houmei/MZ-80K/img/03RAM.png

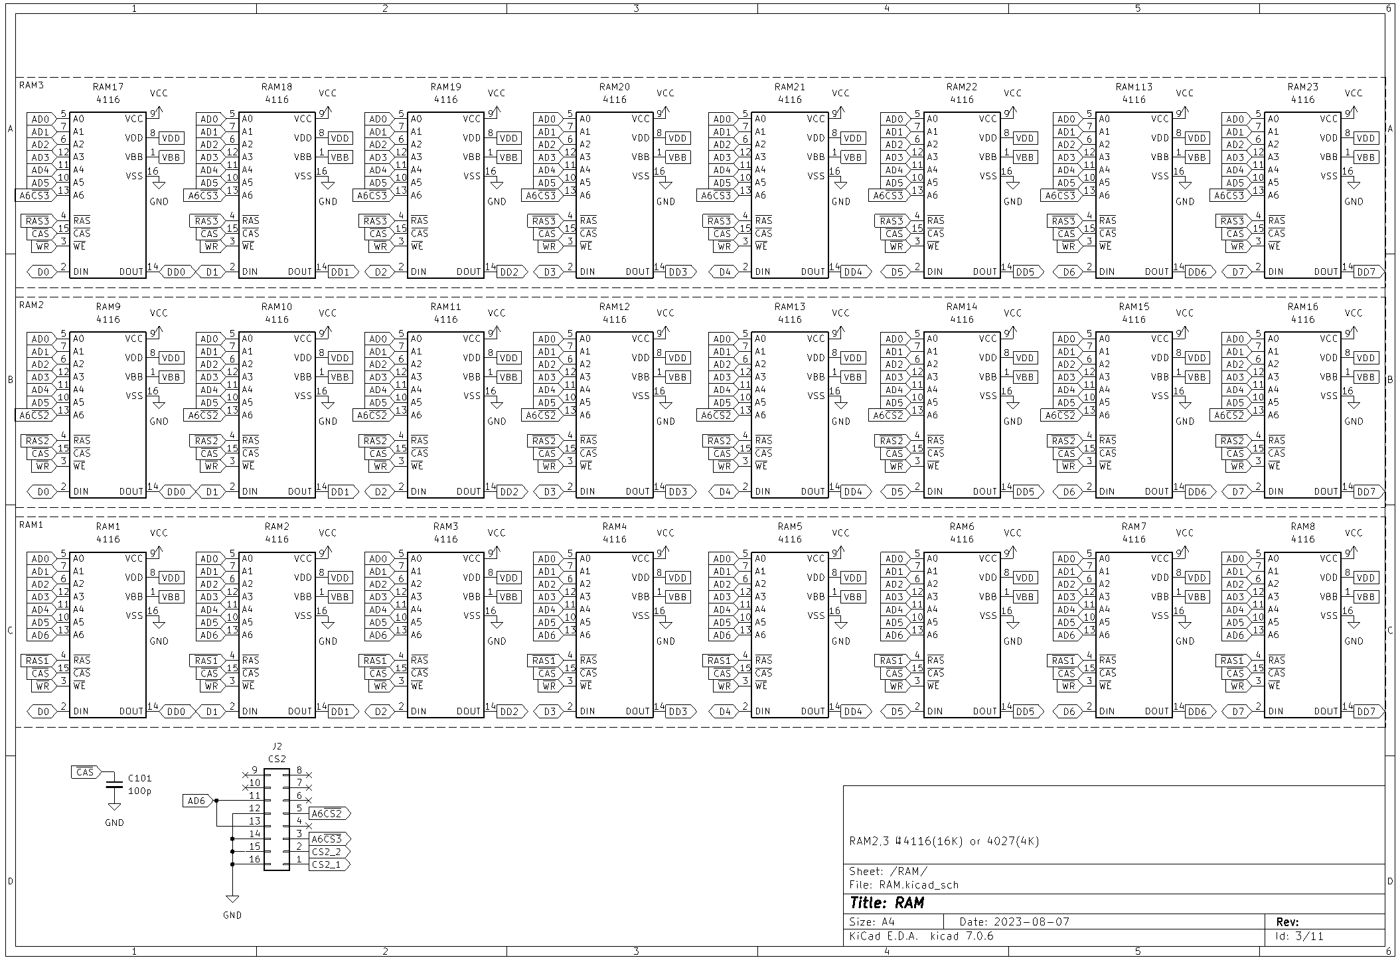
img/03RAM.png
