houmei/MZ-80K/img/05DECODE.png

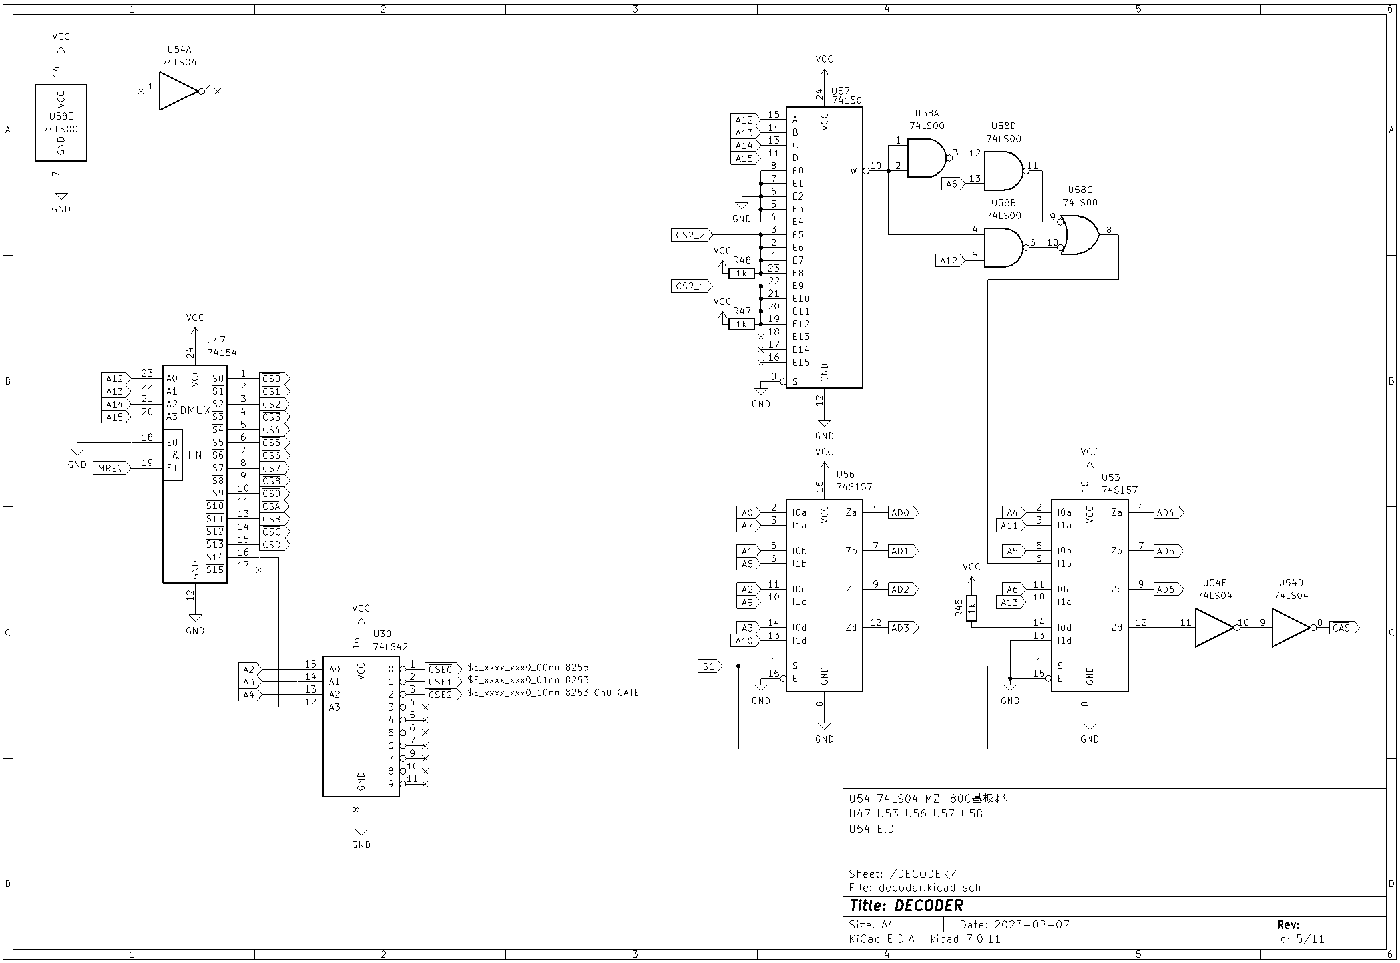
img/05DECODE.png
