houmei/MZ-80K/img/06SYNC.png

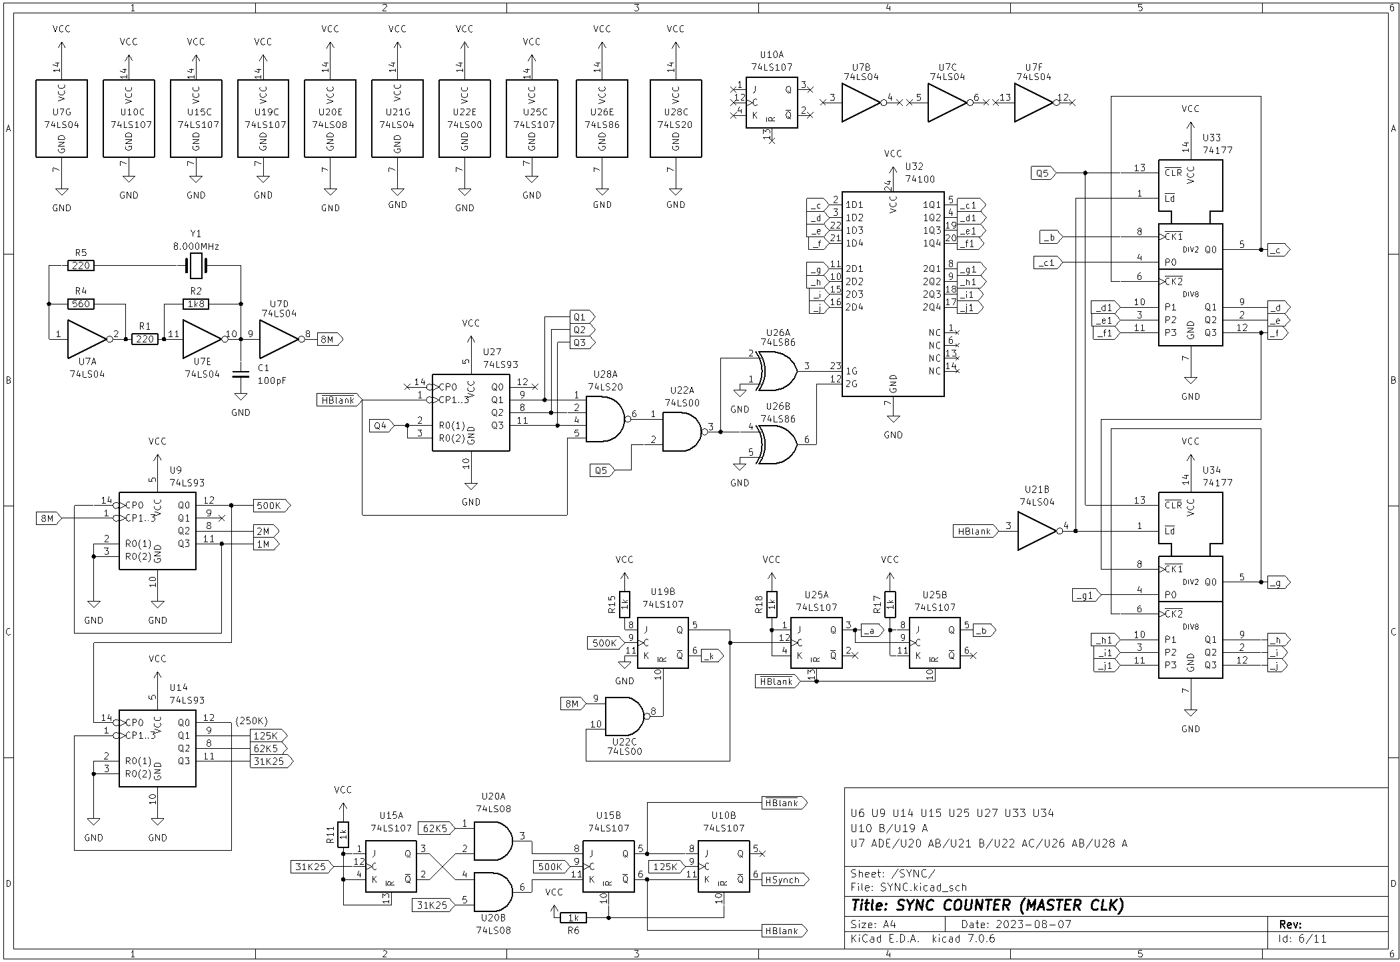
img/06SYNC.png
