houmei/MZ-80K/img/11CONN.png

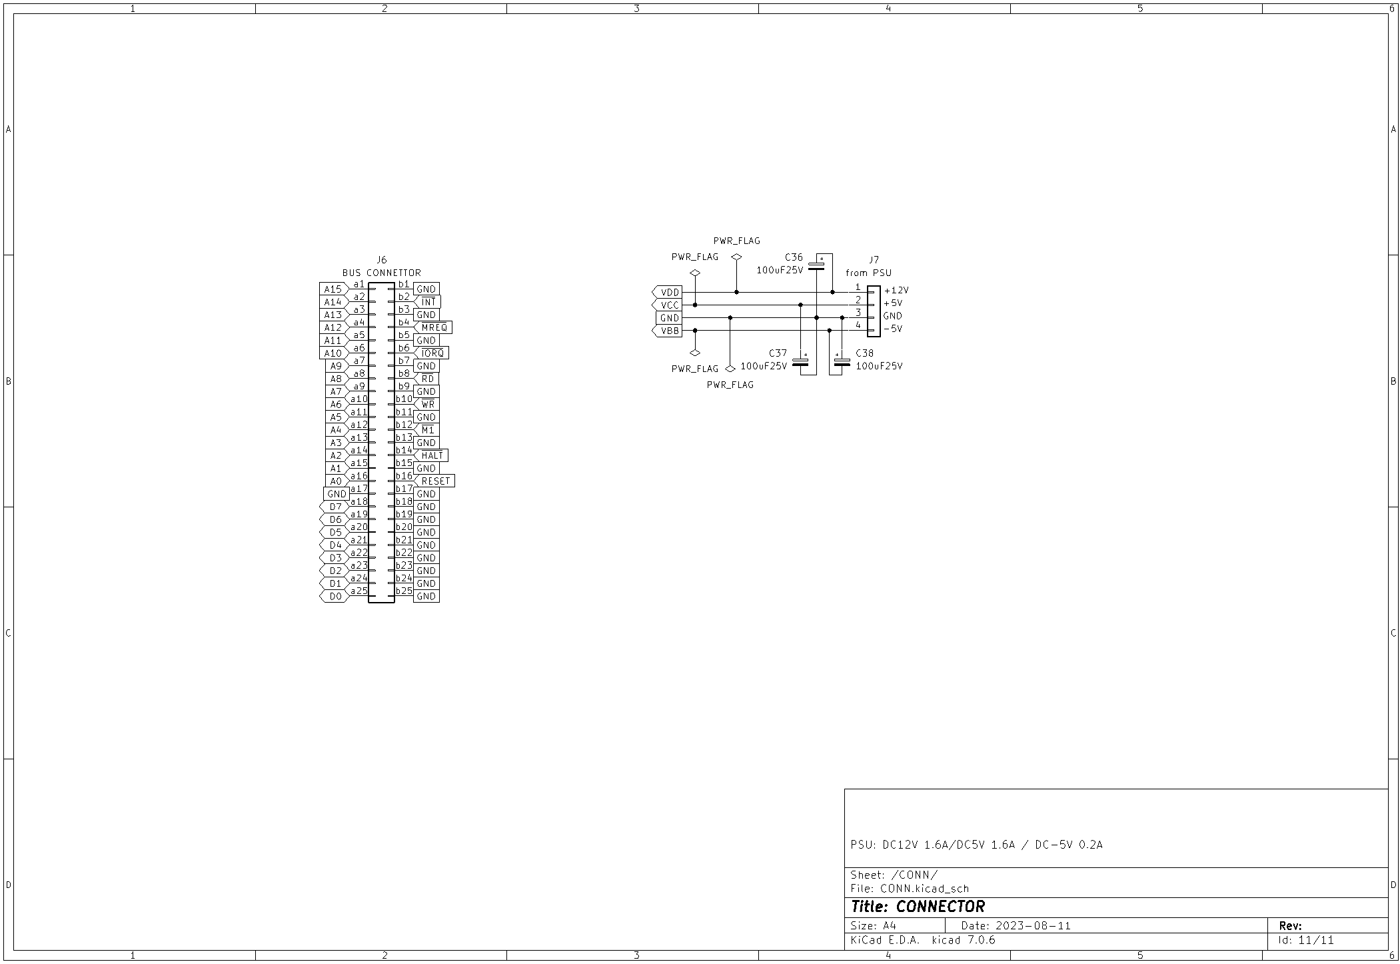
img/11CONN.png
