houmei/MZ-80K/MZ80KiCad/CONN.kicad_sch

## KiCad design MZ80KiCad/CONN.kicad_sch (2023-08-20)

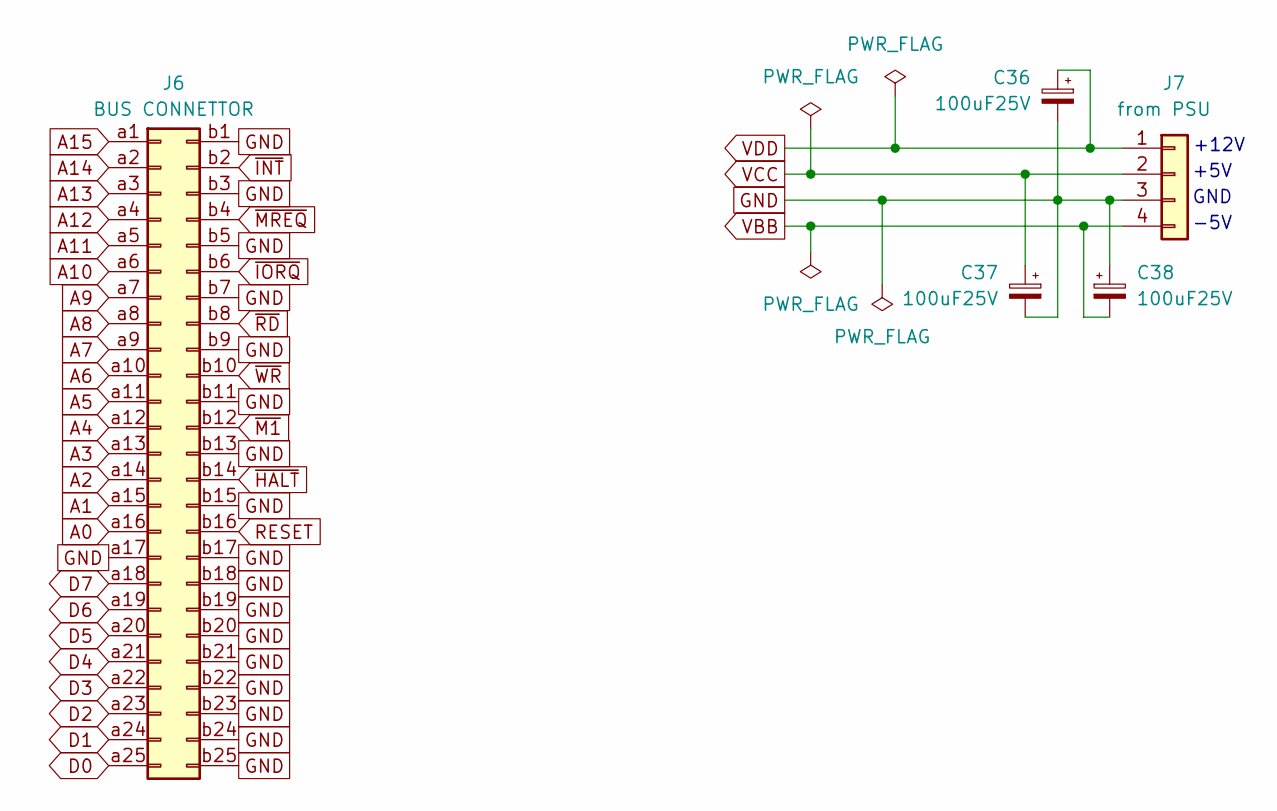
[picture p22: schematic CONN.kicad_sch]

Parts:
C36, C37, C38: 100uF25V
J6: BUS CONNETTOR; PinHeader_2x26_P2.54mm_Horizontal
J7: from PSU; PinHeader_1x04_P2.54mm_Vertical

Connections:
A0: J6.a16
A1: J6.a15
A2: J6.a14
A3: J6.a13
A4: J6.a12
A5: J6.a11
A6: J6.a10
A7: J6.a9
A8: J6.a8
A9: J6.a7
A10: J6.a6
A11: J6.a5
A12: J6.a4
A13: J6.a3
A14: J6.a2
A15: J6.a1
D0: J6.a25
D1: J6.a24
D2: J6.a23
D3: J6.a22
D4: J6.a21
D5: J6.a20
D6: J6.a19
D7: J6.a18
GND: C36.2, C37.2, C38.1, J6.a17, J6.b1, J6.b3, J6.b5, J6.b7, J6.b9, J6.b11, J6.b13, J6.b15, J6.b17, J6.b18, J6.b19, J6.b20, J6.b21, J6.b22, J6.b23, J6.b24, J6.b25, J7.3
RESET: J6.b16
VBB: C38.2, J7.4
VCC: C37.1, J7.2
VDD: C36.1, J7.1
~HALT: J6.b14
~INT: J6.b2
~IORQ: J6.b6
~M1: J6.b12
~MREQ: J6.b4
~RD: J6.b8
~WR: J6.b10

Notes on the sheet:
+5V
+12V
-5V
GND
