houmei/MZ-80K/MZ80KiCad/CPU.kicad_sch

## KiCad design MZ80KiCad/CPU.kicad_sch (2024-05-27)

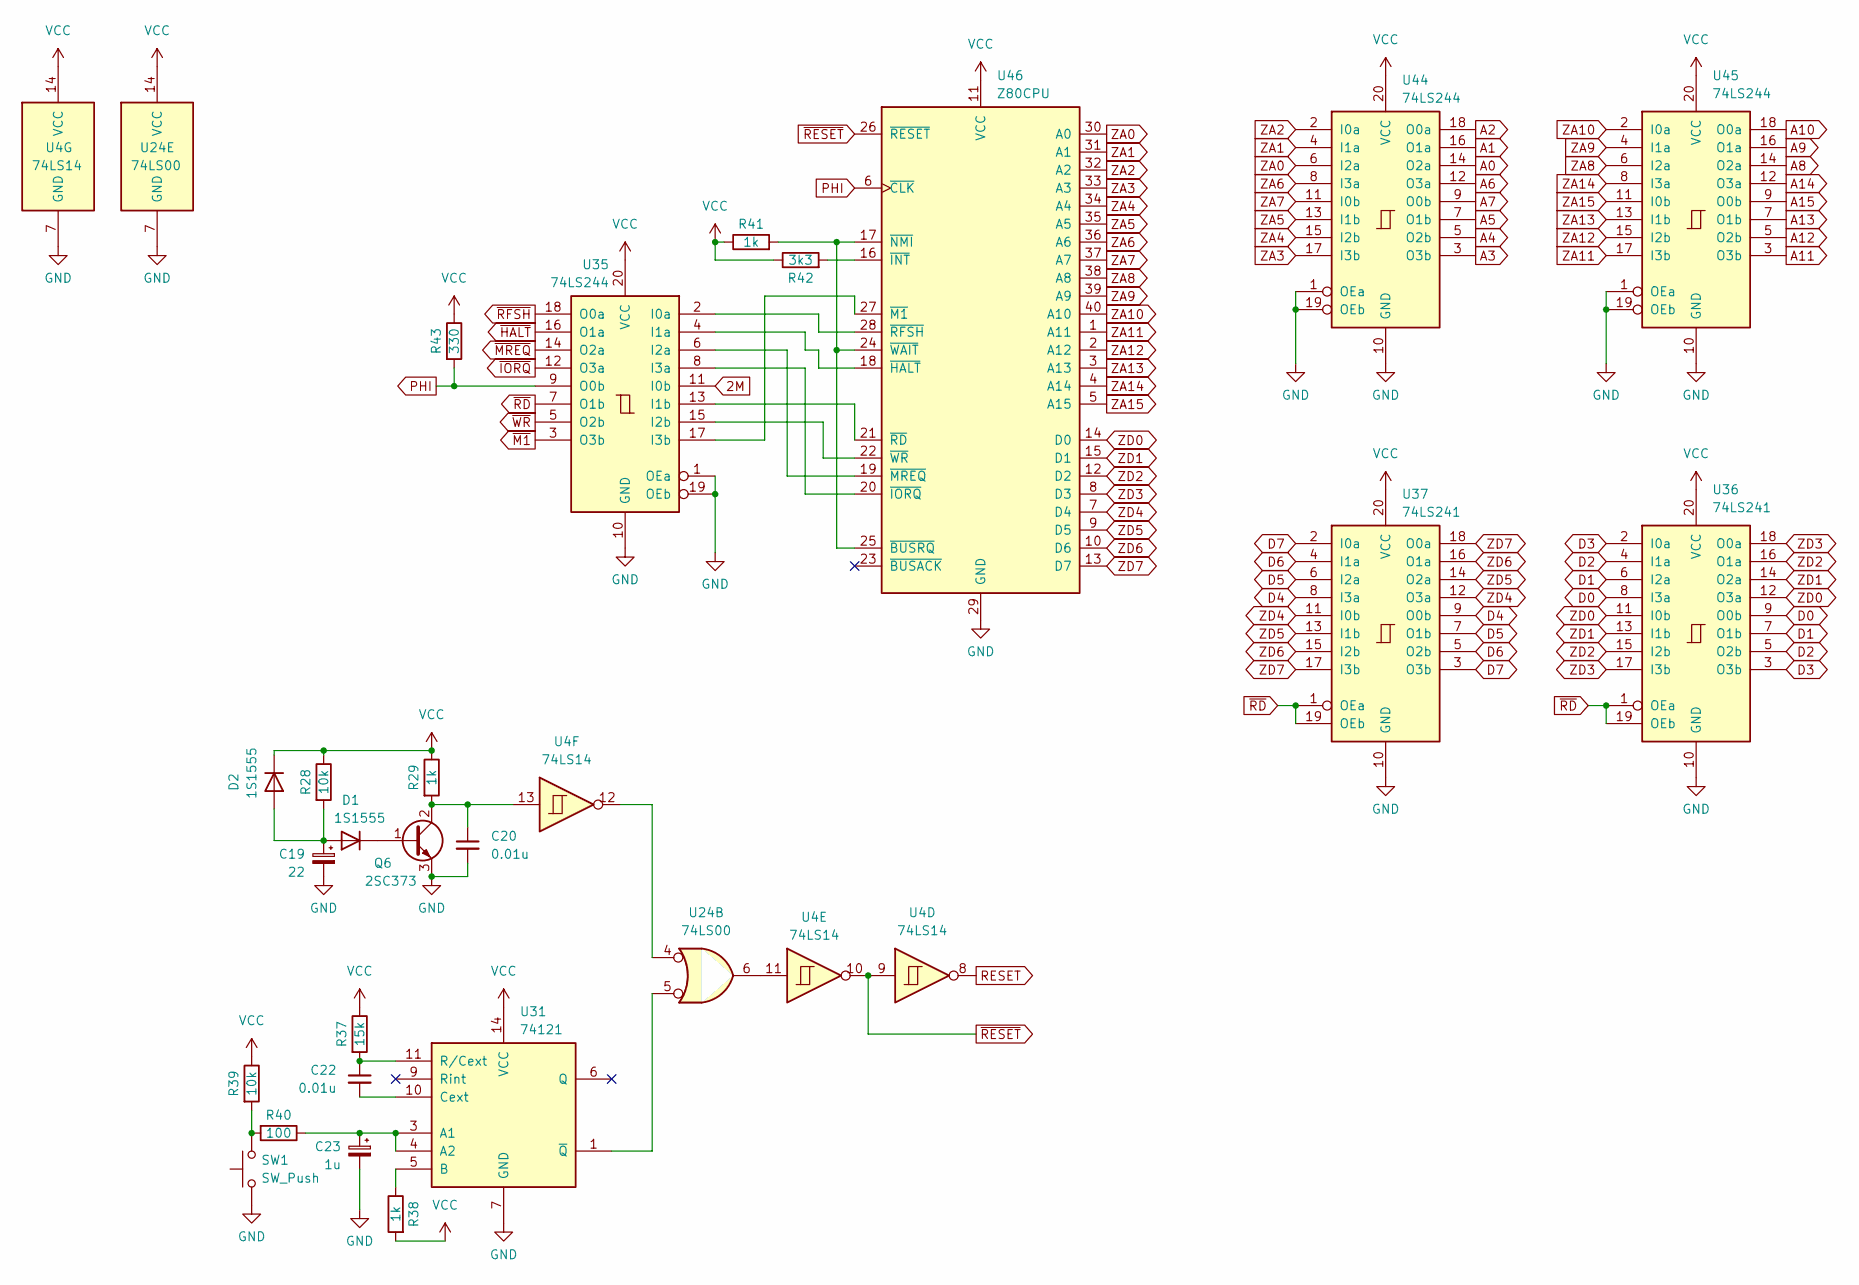
[picture p23: schematic CPU.kicad_sch]

Parts:
C19: 22
C20, C22: 0.01u
C23: 1u
D1, D2: 1S1555; D_DO-41_SOD81_P10.16mm_Horizontal
Q6: 2SC373
R28, R39: 10k
R29, R38, R41: 1k
R37: 15k
R40: 100
R42: 3k3
R43: 330
SW1: SW_Push
U4: 74LS14; DIP-14_W7.62mm
U24: 74LS00; DIP-14_W7.62mm
U31: 74121; DIP-10_W7.62mm
U35, U44, U45: 74LS244; DIP-20_W7.62mm
U36, U37: 74LS241; DIP-20_W7.62mm
U46: Z80CPU; DIP-40_W15.24mm

Connections:
2M: U35.11 (I0b)
A0: U44.14 (O2a)
A1: U44.16 (O1a)
A2: U44.18 (O0a)
A3: U44.3 (O3b)
A4: U44.5 (O2b)
A5: U44.7 (O1b)
A6: U44.12 (O3a)
A7: U44.9 (O0b)
A8: U45.14 (O2a)
A9: U45.16 (O1a)
A10: U45.18 (O0a)
A11: U45.3 (O3b)
A12: U45.5 (O2b)
A13: U45.7 (O1b)
A14: U45.12 (O3a)
A15: U45.9 (O0b)
D0: U36.8 (I3a), U36.9 (O0b)
D1: U36.6 (I2a), U36.7 (O1b)
D2: U36.4 (I1a), U36.5 (O2b)
D3: U36.2 (I0a), U36.3 (O3b)
D4: U37.8 (I3a), U37.9 (O0b)
D5: U37.6 (I2a), U37.7 (O1b)
D6: U37.4 (I1a), U37.5 (O2b)
D7: U37.2 (I0a), U37.3 (O3b)
GND: C19.2, C20.2, C23.2, Q6.3 (E), SW1.1, U4.7 (GND), U24.7 (GND), U31.7 (GND), U35.1 (OEa), U35.10 (GND), U35.19 (OEb), U36.10 (GND), U37.10 (GND), U44.1 (OEa), U44.10 (GND), U44.19 (OEb), U45.1 (OEa), U45.10 (GND), U45.19 (OEb), U46.29 (GND)
unnamed: C19.1, D1.2 (A), D2.2 (A), R28.2
unnamed: C20.1, Q6.2 (C), R29.2, U4.13
unnamed: C22.1, R37.2, U31.11 (R/Cext)
unnamed: C22.2, U31.10 (Cext)
unnamed: C23.1, R40.1, U31.3 (A1), U31.4 (A2)
unnamed: D1.1 (K), Q6.1 (B)
unnamed: R38.1, U31.5 (B)
unnamed: R39.2, R40.2, SW1.2
unnamed: R41.2, U46.17 (~NMI), U46.24 (~WAIT), U46.25 (~BUSRQ)
unnamed: R42.2, U46.16 (~INT)
unnamed: U4.12, U24.4
unnamed: U24.5, U31.1 (~Q)
unnamed: U4.11, U24.6
unnamed: U35.2 (I0a), U46.28 (~RFSH)
unnamed: U35.4 (I1a), U46.18 (~HALT)
unnamed: U35.6 (I2a), U46.19 (~MREQ)
unnamed: U35.8 (I3a), U46.20 (~IORQ)
unnamed: U35.13 (I1b), U46.21 (~RD)
unnamed: U35.15 (I2b), U46.22 (~WR)
unnamed: U35.17 (I3b), U46.27 (~M1)
PHI: R43.2, U35.9 (O0b), U46.6 (~CLK)
RESET: U4.8
VCC: D2.1 (K), R28.1, R29.1, R37.1, R38.2, R39.1, R41.1, R42.1, R43.1, U4.14 (VCC), U24.14 (VCC), U31.14 (VCC), U35.20 (VCC), U36.20 (VCC), U37.20 (VCC), U44.20 (VCC), U45.20 (VCC), U46.11 (VCC)
ZA0: U44.6 (I2a), U46.30 (A0)
ZA1: U44.4 (I1a), U46.31 (A1)
ZA2: U44.2 (I0a), U46.32 (A2)
ZA3: U44.17 (I3b), U46.33 (A3)
ZA4: U44.15 (I2b), U46.34 (A4)
ZA5: U44.13 (I1b), U46.35 (A5)
ZA6: U44.8 (I3a), U46.36 (A6)
ZA7: U44.11 (I0b), U46.37 (A7)
ZA8: U45.6 (I2a), U46.38 (A8)
ZA9: U45.4 (I1a), U46.39 (A9)
ZA10: U45.2 (I0a), U46.40 (A10)
ZA11: U45.17 (I3b), U46.1 (A11)
ZA12: U45.15 (I2b), U46.2 (A12)
ZA13: U45.13 (I1b), U46.3 (A13)
ZA14: U45.8 (I3a), U46.4 (A14)
ZA15: U45.11 (I0b), U46.5 (A15)
ZD0: U36.11 (I0b), U36.12 (O3a), U46.14 (D0)
ZD1: U36.13 (I1b), U36.14 (O2a), U46.15 (D1)
ZD2: U36.15 (I2b), U36.16 (O1a), U46.12 (D2)
ZD3: U36.17 (I3b), U36.18 (O0a), U46.8 (D3)
ZD4: U37.11 (I0b), U37.12 (O3a), U46.7 (D4)
ZD5: U37.13 (I1b), U37.14 (O2a), U46.9 (D5)
ZD6: U37.15 (I2b), U37.16 (O1a), U46.10 (D6)
ZD7: U37.17 (I3b), U37.18 (O0a), U46.13 (D7)
~HALT: U35.16 (O1a)
~IORQ: U35.12 (O3a)
~M1: U35.3 (O3b)
~MREQ: U35.14 (O2a)
~RD: U35.7 (O1b), U36.1 (OEa), U36.19 (OEb), U37.1 (OEa), U37.19 (OEb)
~RESET: U4.9, U4.10, U46.26 (~RESET)
~RFSH: U35.18 (O0a)
~WR: U35.5 (O2b)
