houmei/MZ-80K/MZ80KiCad/PPI.kicad_sch

## KiCad design MZ80KiCad/PPI.kicad_sch (2024-05-27)

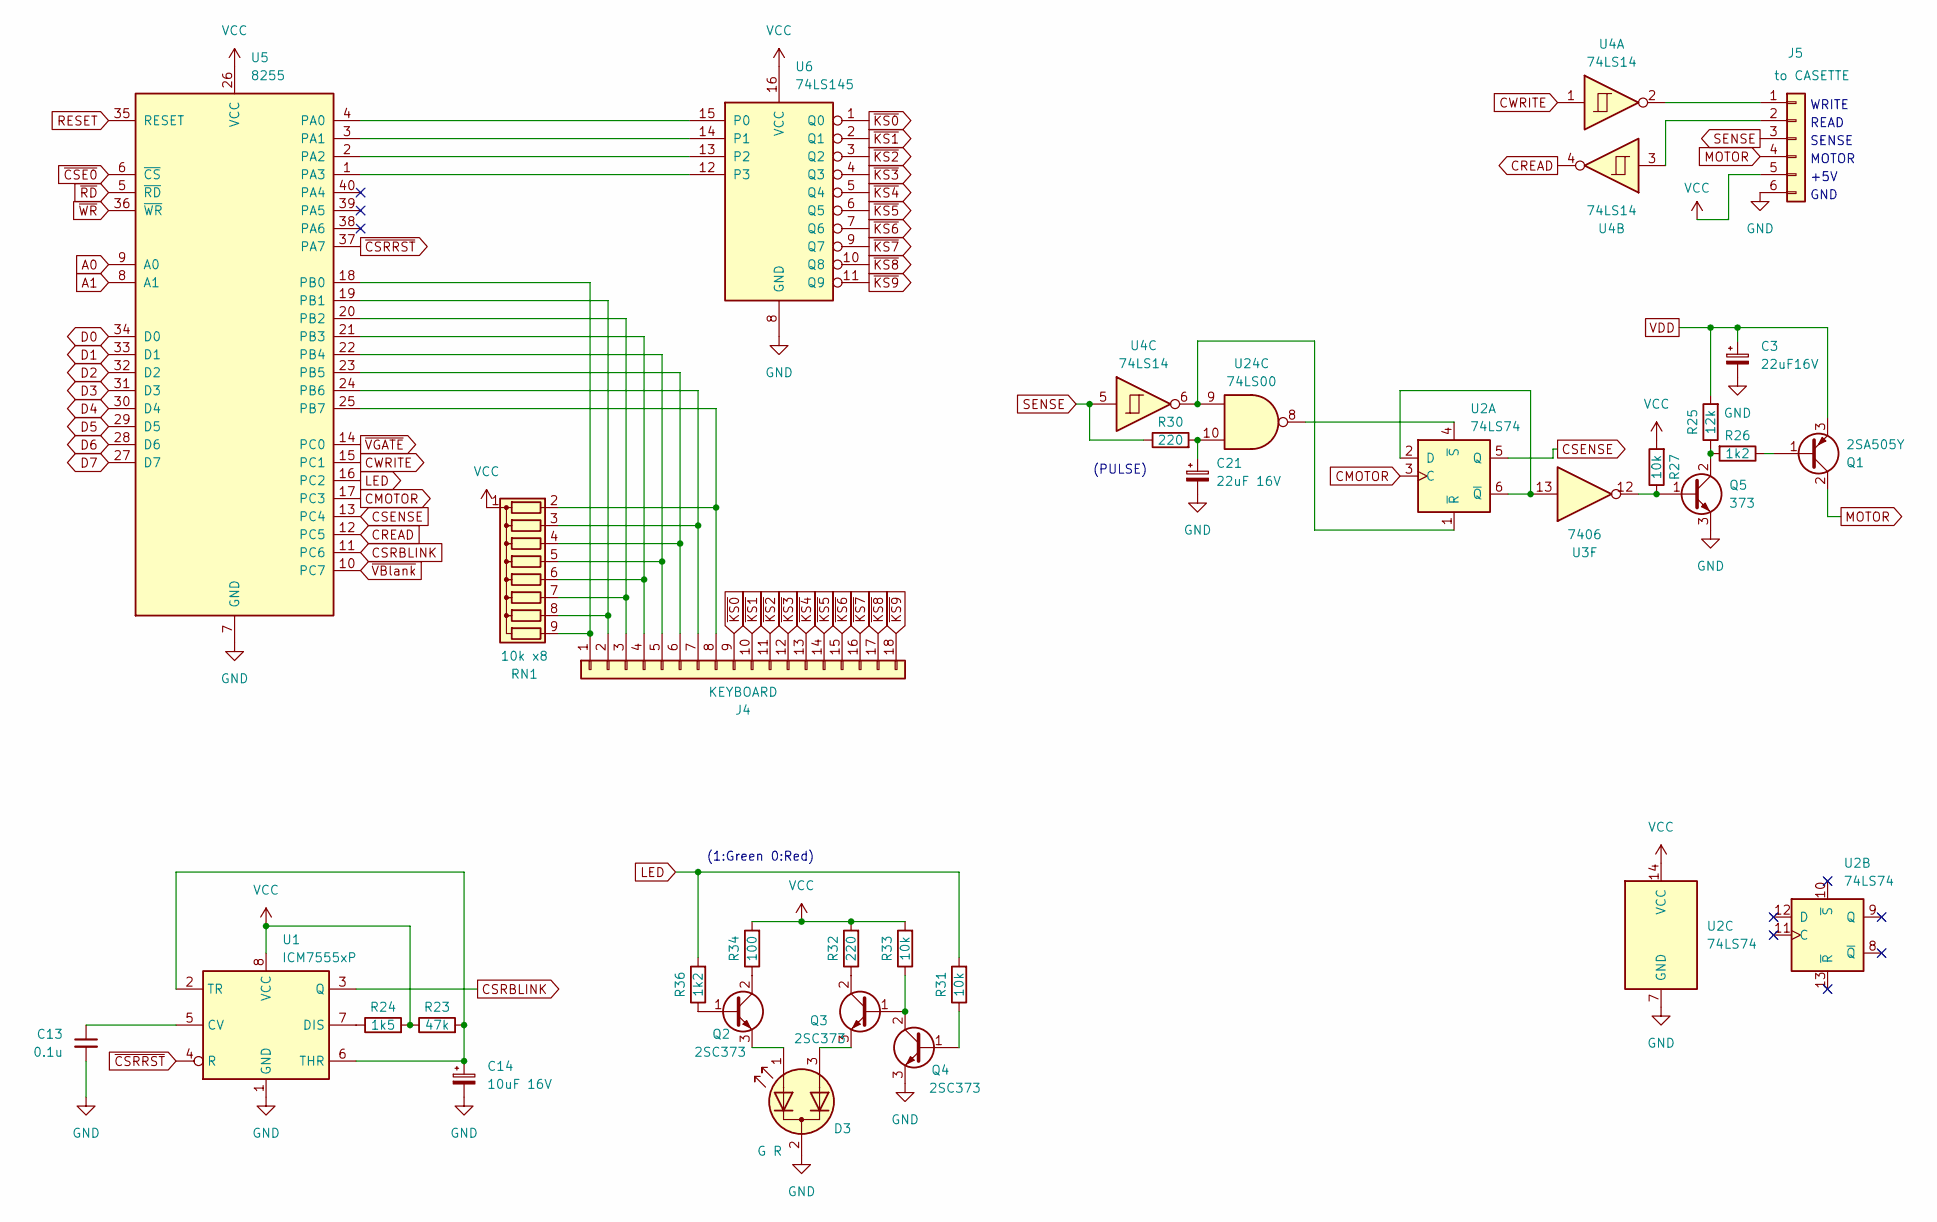
[picture p24: schematic PPI.kicad_sch]

Parts:
C3: 22uF16V
C13: 0.1u
C14: 10uF 16V
C21: 22uF 16V
D3: G R
J4: KEYBOARD; PinHeader_1x18_P2.54mm_Vertical
J5: to CASETTE; PinHeader_1x06_P2.54mm_Vertical
Q1: 2SA505Y
Q2, Q3, Q4: 2SC373
Q5: 373
R23: 47k
R24: 1k5
R25: 12k
R26, R36: 1k2
R27, R31, R33: 10k
R30, R32: 220
R34: 100
RN1: 10k x8; R_Array_SIP9
U1: ICM7555xP; DIP-8_W7.62mm
U2: 74LS74; DIP-14_W7.62mm
U3: 7406; DIP-14_W7.62mm
U4: 74LS14; DIP-14_W7.62mm
U5: 8255; DIP-40_W15.24mm
U6: 74LS145; DIP-16_W7.62mm
U24: 74LS00; DIP-14_W7.62mm

Connections:
A0: U5.9 (A0)
A1: U5.8 (A1)
CMOTOR: U2.3 (C), U5.17 (PC3)
CREAD: U4.4, U5.12 (PC5)
CSENSE: U2.5 (Q), U5.13 (PC4)
CSRBLINK: U1.3 (Q), U5.11 (PC6)
CWRITE: U4.1, U5.15 (PC1)
D0: U5.34 (D0)
D1: U5.33 (D1)
D2: U5.32 (D2)
D3: U5.31 (D3)
D4: U5.30 (D4)
D5: U5.29 (D5)
D6: U5.28 (D6)
D7: U5.27 (D7)
GND: C3.2, C13.2, C14.2, C21.2, D3.2 (K), J5.6, Q4.3 (E), Q5.3 (E), U1.1 (GND), U2.7 (GND), U5.7 (GND), U6.8 (GND)
LED: R31.2, R36.2, U5.16 (PC2)
MOTOR: J5.4, Q1.2 (C)
unnamed: C13.1, U1.5 (CV)
unnamed: C14.1, R23.2, U1.2 (TR), U1.6 (THR)
unnamed: C21.1, R30.2, U24.10
unnamed: D3.1 (A1), Q2.3 (E)
unnamed: D3.3 (A2), Q3.3 (E)
unnamed: J4.1, RN1.9 (R8), U5.18 (PB0)
unnamed: J4.2, RN1.8 (R7), U5.19 (PB1)
unnamed: J4.3, RN1.7 (R6), U5.20 (PB2)
unnamed: J4.4, RN1.6 (R5), U5.21 (PB3)
unnamed: J4.5, RN1.5 (R4), U5.22 (PB4)
unnamed: J4.6, RN1.4 (R3), U5.23 (PB5)
unnamed: J4.7, RN1.3 (R2), U5.24 (PB6)
unnamed: J4.8, RN1.2 (R1), U5.25 (PB7)
unnamed: J5.1, U4.2
unnamed: J5.2, U4.3
unnamed: Q1.1 (B), R26.1
unnamed: Q2.1 (B), R36.1
unnamed: Q2.2 (C), R34.1
unnamed: Q3.1 (B), Q4.2 (C), R33.1
unnamed: Q3.2 (C), R32.1
unnamed: Q4.1 (B), R31.1
unnamed: Q5.1 (B), R27.1, U3.12
unnamed: Q5.2 (C), R25.1, R26.2
unnamed: R24.1, U1.7 (DIS)
unnamed: U2.1 (~R), U4.6, U24.9
unnamed: U2.2 (D), U2.6 (~Q), U3.13
unnamed: U2.4 (~S), U24.8
unnamed: U5.1 (PA3), U6.12 (P3)
unnamed: U5.2 (PA2), U6.13 (P2)
unnamed: U5.3 (PA1), U6.14 (P1)
unnamed: U5.4 (PA0), U6.15 (P0)
RESET: U5.35 (RESET)
SENSE: J5.3, R30.1, U4.5
VCC: J5.5, R23.1, R24.2, R27.2, R32.2, R33.2, R34.2, RN1.1 (common), U1.8 (VCC), U2.14 (VCC), U5.26 (VCC), U6.16 (VCC)
VDD: C3.1, Q1.3 (E), R25.2
~CSE0: U5.6 (~CS)
~CSRRST: U1.4 (R), U5.37 (PA7)
~KS0: J4.9, U6.1 (Q0)
~KS1: J4.10, U6.2 (Q1)
~KS2: J4.11, U6.3 (Q2)
~KS3: J4.12, U6.4 (Q3)
~KS4: J4.13, U6.5 (Q4)
~KS5: J4.14, U6.6 (Q5)
~KS6: J4.15, U6.7 (Q6)
~KS7: J4.16, U6.9 (Q7)
~KS8: J4.17, U6.10 (Q8)
~KS9: J4.18, U6.11 (Q9)
~RD: U5.5 (~RD)
~VBlank: U5.10 (PC7)
~VGATE: U5.14 (PC0)
~WR: U5.36 (~WR)

Notes on the sheet:
GND
(1:Green 0:Red)
READ
WRITE
+5V
SENSE
(PULSE)
MOTOR
