houmei/MZ-80K/MZ80KiCad/RAM.kicad_sch

## KiCad design MZ80KiCad/RAM.kicad_sch (2023-08-20)

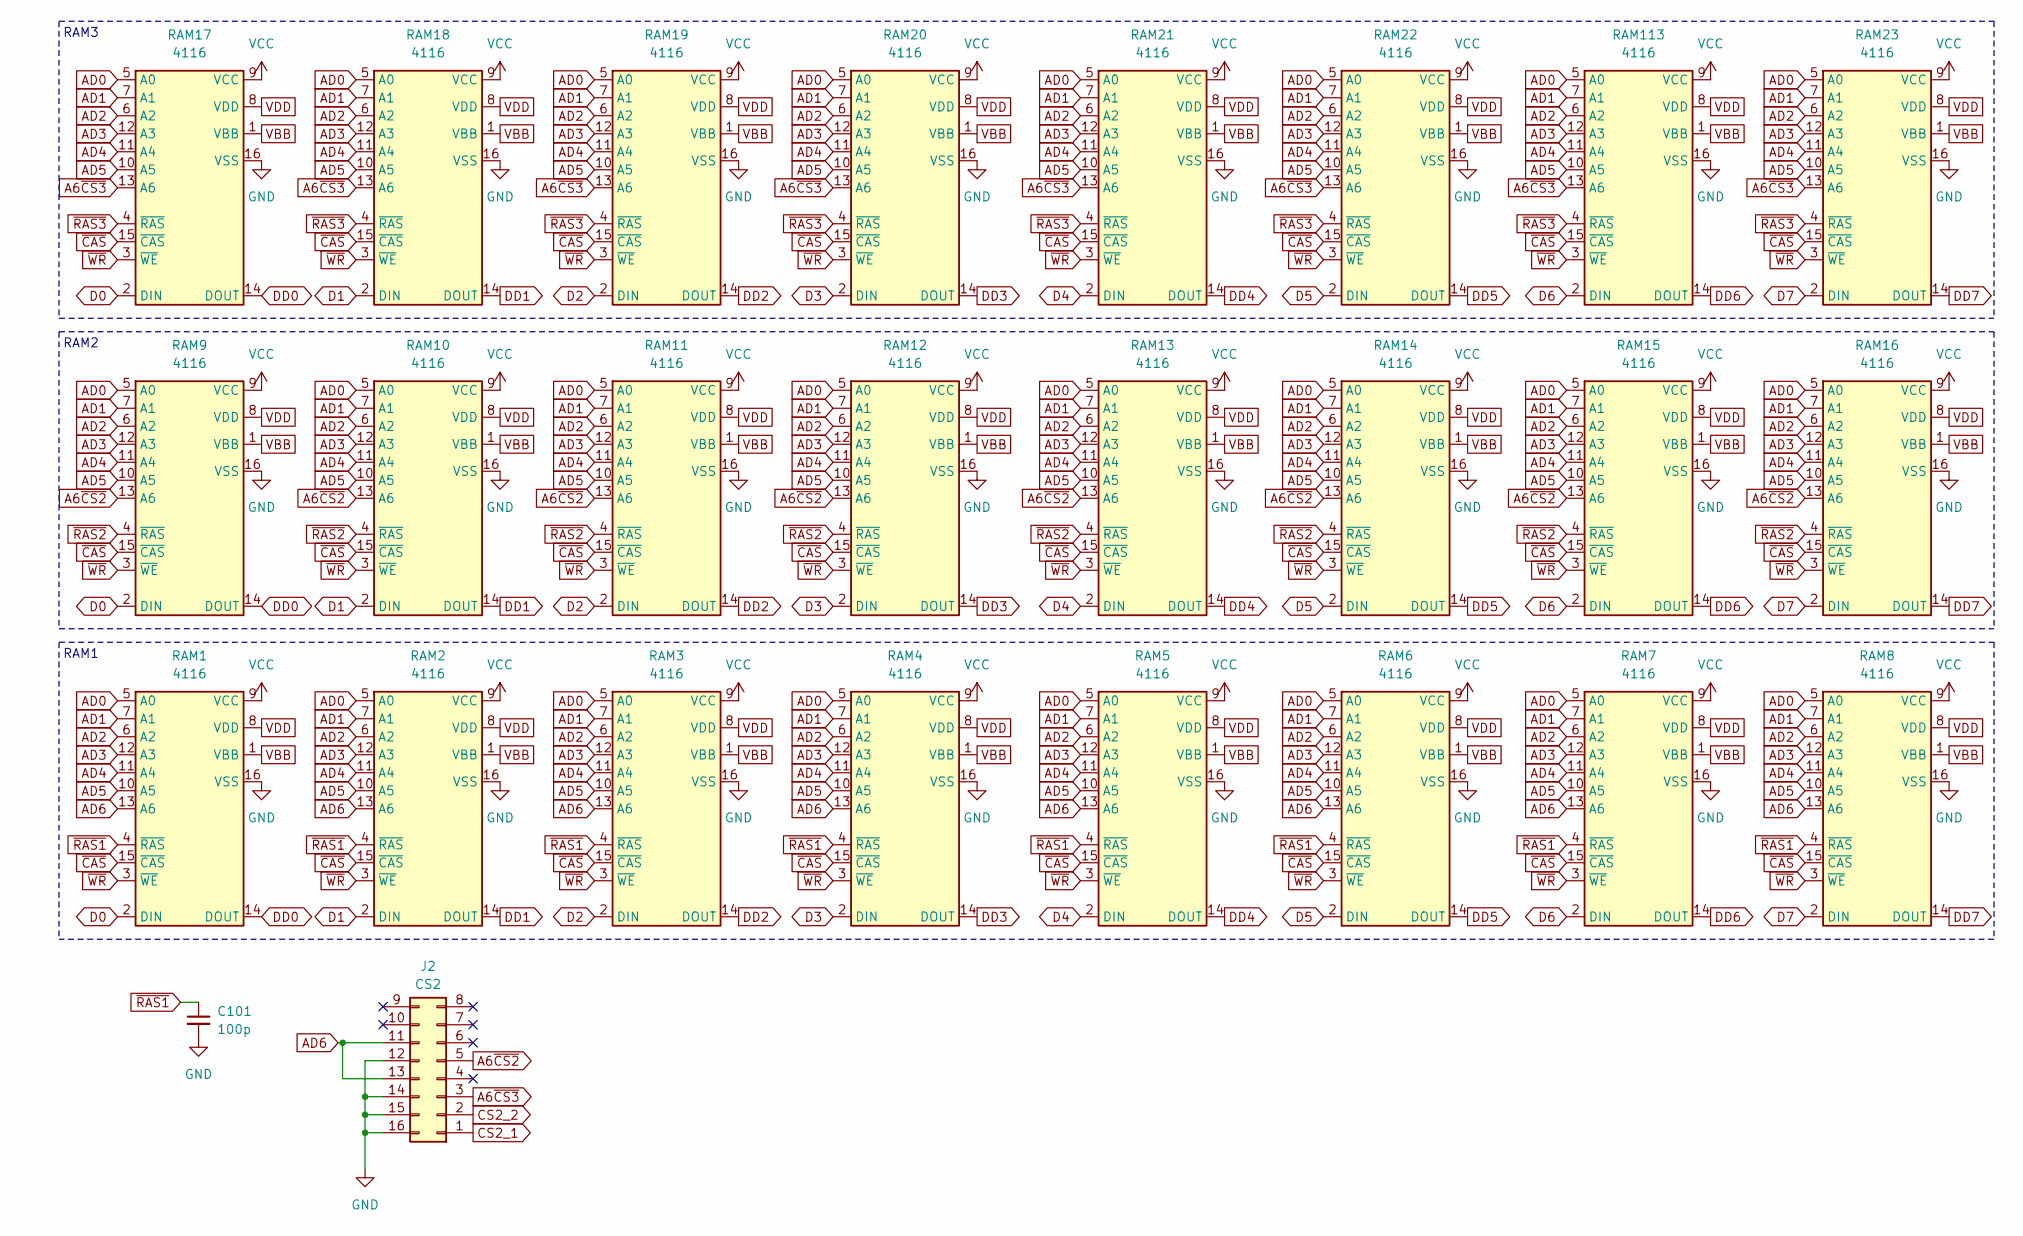
[picture p25: schematic RAM.kicad_sch]

Parts:
C101: 100p
J2: CS2
RAM1, RAM2, RAM3, RAM4, RAM5, RAM6, RAM7, RAM8, RAM9, RAM10, RAM11, RAM12, RAM13, RAM14, RAM15, RAM16, RAM17, RAM18, RAM19, RAM20, RAM21, RAM22, RAM23, RAM113: 4116; DIP-16_W7.62mm

Connections:
A6~CS2: J2.5, RAM9.13 (A6), RAM10.13 (A6), RAM11.13 (A6), RAM12.13 (A6), RAM13.13 (A6), RAM14.13 (A6), RAM15.13 (A6), RAM16.13 (A6)
A6~CS3: J2.3, RAM17.13 (A6), RAM18.13 (A6), RAM19.13 (A6), RAM20.13 (A6), RAM21.13 (A6), RAM22.13 (A6), RAM23.13 (A6), RAM113.13 (A6)
AD0: RAM1.5 (A0), RAM2.5 (A0), RAM3.5 (A0), RAM4.5 (A0), RAM5.5 (A0), RAM6.5 (A0), RAM7.5 (A0), RAM8.5 (A0), RAM9.5 (A0), RAM10.5 (A0), RAM11.5 (A0), RAM12.5 (A0), RAM13.5 (A0), RAM14.5 (A0), RAM15.5 (A0), RAM16.5 (A0), RAM17.5 (A0), RAM18.5 (A0), RAM19.5 (A0), RAM20.5 (A0), RAM21.5 (A0), RAM22.5 (A0), RAM23.5 (A0), RAM113.5 (A0)
AD1: RAM1.7 (A1), RAM2.7 (A1), RAM3.7 (A1), RAM4.7 (A1), RAM5.7 (A1), RAM6.7 (A1), RAM7.7 (A1), RAM8.7 (A1), RAM9.7 (A1), RAM10.7 (A1), RAM11.7 (A1), RAM12.7 (A1), RAM13.7 (A1), RAM14.7 (A1), RAM15.7 (A1), RAM16.7 (A1), RAM17.7 (A1), RAM18.7 (A1), RAM19.7 (A1), RAM20.7 (A1), RAM21.7 (A1), RAM22.7 (A1), RAM23.7 (A1), RAM113.7 (A1)
AD2: RAM1.6 (A2), RAM2.6 (A2), RAM3.6 (A2), RAM4.6 (A2), RAM5.6 (A2), RAM6.6 (A2), RAM7.6 (A2), RAM8.6 (A2), RAM9.6 (A2), RAM10.6 (A2), RAM11.6 (A2), RAM12.6 (A2), RAM13.6 (A2), RAM14.6 (A2), RAM15.6 (A2), RAM16.6 (A2), RAM17.6 (A2), RAM18.6 (A2), RAM19.6 (A2), RAM20.6 (A2), RAM21.6 (A2), RAM22.6 (A2), RAM23.6 (A2), RAM113.6 (A2)
AD3: RAM1.12 (A3), RAM2.12 (A3), RAM3.12 (A3), RAM4.12 (A3), RAM5.12 (A3), RAM6.12 (A3), RAM7.12 (A3), RAM8.12 (A3), RAM9.12 (A3), RAM10.12 (A3), RAM11.12 (A3), RAM12.12 (A3), RAM13.12 (A3), RAM14.12 (A3), RAM15.12 (A3), RAM16.12 (A3), RAM17.12 (A3), RAM18.12 (A3), RAM19.12 (A3), RAM20.12 (A3), RAM21.12 (A3), RAM22.12 (A3), RAM23.12 (A3), RAM113.12 (A3)
AD4: RAM1.11 (A4), RAM2.11 (A4), RAM3.11 (A4), RAM4.11 (A4), RAM5.11 (A4), RAM6.11 (A4), RAM7.11 (A4), RAM8.11 (A4), RAM9.11 (A4), RAM10.11 (A4), RAM11.11 (A4), RAM12.11 (A4), RAM13.11 (A4), RAM14.11 (A4), RAM15.11 (A4), RAM16.11 (A4), RAM17.11 (A4), RAM18.11 (A4), RAM19.11 (A4), RAM20.11 (A4), RAM21.11 (A4), RAM22.11 (A4), RAM23.11 (A4), RAM113.11 (A4)
AD5: RAM1.10 (A5), RAM2.10 (A5), RAM3.10 (A5), RAM4.10 (A5), RAM5.10 (A5), RAM6.10 (A5), RAM7.10 (A5), RAM8.10 (A5), RAM9.10 (A5), RAM10.10 (A5), RAM11.10 (A5), RAM12.10 (A5), RAM13.10 (A5), RAM14.10 (A5), RAM15.10 (A5), RAM16.10 (A5), RAM17.10 (A5), RAM18.10 (A5), RAM19.10 (A5), RAM20.10 (A5), RAM21.10 (A5), RAM22.10 (A5), RAM23.10 (A5), RAM113.10 (A5)
AD6: J2.11, J2.13, RAM1.13 (A6), RAM2.13 (A6), RAM3.13 (A6), RAM4.13 (A6), RAM5.13 (A6), RAM6.13 (A6), RAM7.13 (A6), RAM8.13 (A6)
CS2_1: J2.1
CS2_2: J2.2
D0: RAM1.2 (DIN), RAM9.2 (DIN), RAM17.2 (DIN)
D1: RAM2.2 (DIN), RAM10.2 (DIN), RAM18.2 (DIN)
D2: RAM3.2 (DIN), RAM11.2 (DIN), RAM19.2 (DIN)
D3: RAM4.2 (DIN), RAM12.2 (DIN), RAM20.2 (DIN)
D4: RAM5.2 (DIN), RAM13.2 (DIN), RAM21.2 (DIN)
D5: RAM6.2 (DIN), RAM14.2 (DIN), RAM22.2 (DIN)
D6: RAM7.2 (DIN), RAM15.2 (DIN), RAM113.2 (DIN)
D7: RAM8.2 (DIN), RAM16.2 (DIN), RAM23.2 (DIN)
DD0: RAM1.14 (DOUT), RAM9.14 (DOUT), RAM17.14 (DOUT)
DD1: RAM2.14 (DOUT), RAM10.14 (DOUT), RAM18.14 (DOUT)
DD2: RAM3.14 (DOUT), RAM11.14 (DOUT), RAM19.14 (DOUT)
DD3: RAM4.14 (DOUT), RAM12.14 (DOUT), RAM20.14 (DOUT)
DD4: RAM5.14 (DOUT), RAM13.14 (DOUT), RAM21.14 (DOUT)
DD5: RAM6.14 (DOUT), RAM14.14 (DOUT), RAM22.14 (DOUT)
DD6: RAM7.14 (DOUT), RAM15.14 (DOUT), RAM113.14 (DOUT)
DD7: RAM8.14 (DOUT), RAM16.14 (DOUT), RAM23.14 (DOUT)
GND: C101.2, J2.12, J2.14, J2.15, J2.16, RAM1.16 (VSS), RAM2.16 (VSS), RAM3.16 (VSS), RAM4.16 (VSS), RAM5.16 (VSS), RAM6.16 (VSS), RAM7.16 (VSS), RAM8.16 (VSS), RAM9.16 (VSS), RAM10.16 (VSS), RAM11.16 (VSS), RAM12.16 (VSS), RAM13.16 (VSS), RAM14.16 (VSS), RAM15.16 (VSS), RAM16.16 (VSS), RAM17.16 (VSS), RAM18.16 (VSS), RAM19.16 (VSS), RAM20.16 (VSS), RAM21.16 (VSS), RAM22.16 (VSS), RAM23.16 (VSS), RAM113.16 (VSS)
VBB: RAM1.1 (VBB), RAM2.1 (VBB), RAM3.1 (VBB), RAM4.1 (VBB), RAM5.1 (VBB), RAM6.1 (VBB), RAM7.1 (VBB), RAM8.1 (VBB), RAM9.1 (VBB), RAM10.1 (VBB), RAM11.1 (VBB), RAM12.1 (VBB), RAM13.1 (VBB), RAM14.1 (VBB), RAM15.1 (VBB), RAM16.1 (VBB), RAM17.1 (VBB), RAM18.1 (VBB), RAM19.1 (VBB), RAM20.1 (VBB), RAM21.1 (VBB), RAM22.1 (VBB), RAM23.1 (VBB), RAM113.1 (VBB)
VCC: RAM1.9 (VCC), RAM2.9 (VCC), RAM3.9 (VCC), RAM4.9 (VCC), RAM5.9 (VCC), RAM6.9 (VCC), RAM7.9 (VCC), RAM8.9 (VCC), RAM9.9 (VCC), RAM10.9 (VCC), RAM11.9 (VCC), RAM12.9 (VCC), RAM13.9 (VCC), RAM14.9 (VCC), RAM15.9 (VCC), RAM16.9 (VCC), RAM17.9 (VCC), RAM18.9 (VCC), RAM19.9 (VCC), RAM20.9 (VCC), RAM21.9 (VCC), RAM22.9 (VCC), RAM23.9 (VCC), RAM113.9 (VCC)
VDD: RAM1.8 (VDD), RAM2.8 (VDD), RAM3.8 (VDD), RAM4.8 (VDD), RAM5.8 (VDD), RAM6.8 (VDD), RAM7.8 (VDD), RAM8.8 (VDD), RAM9.8 (VDD), RAM10.8 (VDD), RAM11.8 (VDD), RAM12.8 (VDD), RAM13.8 (VDD), RAM14.8 (VDD), RAM15.8 (VDD), RAM16.8 (VDD), RAM17.8 (VDD), RAM18.8 (VDD), RAM19.8 (VDD), RAM20.8 (VDD), RAM21.8 (VDD), RAM22.8 (VDD), RAM23.8 (VDD), RAM113.8 (VDD)
~CAS: RAM1.15 (~CAS), RAM2.15 (~CAS), RAM3.15 (~CAS), RAM4.15 (~CAS), RAM5.15 (~CAS), RAM6.15 (~CAS), RAM7.15 (~CAS), RAM8.15 (~CAS), RAM9.15 (~CAS), RAM10.15 (~CAS), RAM11.15 (~CAS), RAM12.15 (~CAS), RAM13.15 (~CAS), RAM14.15 (~CAS), RAM15.15 (~CAS), RAM16.15 (~CAS), RAM17.15 (~CAS), RAM18.15 (~CAS), RAM19.15 (~CAS), RAM20.15 (~CAS), RAM21.15 (~CAS), RAM22.15 (~CAS), RAM23.15 (~CAS), RAM113.15 (~CAS)
~RAS1: C101.1, RAM1.4 (~RAS), RAM2.4 (~RAS), RAM3.4 (~RAS), RAM4.4 (~RAS), RAM5.4 (~RAS), RAM6.4 (~RAS), RAM7.4 (~RAS), RAM8.4 (~RAS)
~RAS2: RAM9.4 (~RAS), RAM10.4 (~RAS), RAM11.4 (~RAS), RAM12.4 (~RAS), RAM13.4 (~RAS), RAM14.4 (~RAS), RAM15.4 (~RAS), RAM16.4 (~RAS)
~RAS3: RAM17.4 (~RAS), RAM18.4 (~RAS), RAM19.4 (~RAS), RAM20.4 (~RAS), RAM21.4 (~RAS), RAM22.4 (~RAS), RAM23.4 (~RAS), RAM113.4 (~RAS)
~WR: RAM1.3 (~WE), RAM2.3 (~WE), RAM3.3 (~WE), RAM4.3 (~WE), RAM5.3 (~WE), RAM6.3 (~WE), RAM7.3 (~WE), RAM8.3 (~WE), RAM9.3 (~WE), RAM10.3 (~WE), RAM11.3 (~WE), RAM12.3 (~WE), RAM13.3 (~WE), RAM14.3 (~WE), RAM15.3 (~WE), RAM16.3 (~WE), RAM17.3 (~WE), RAM18.3 (~WE), RAM19.3 (~WE), RAM20.3 (~WE), RAM21.3 (~WE), RAM22.3 (~WE), RAM23.3 (~WE), RAM113.3 (~WE)

Notes on the sheet:
RAM3
RAM1
RAM2
