houmei/MZ-80K/MZ80KiCad/SYNC.kicad_sch

## KiCad design MZ80KiCad/SYNC.kicad_sch (2023-08-20)

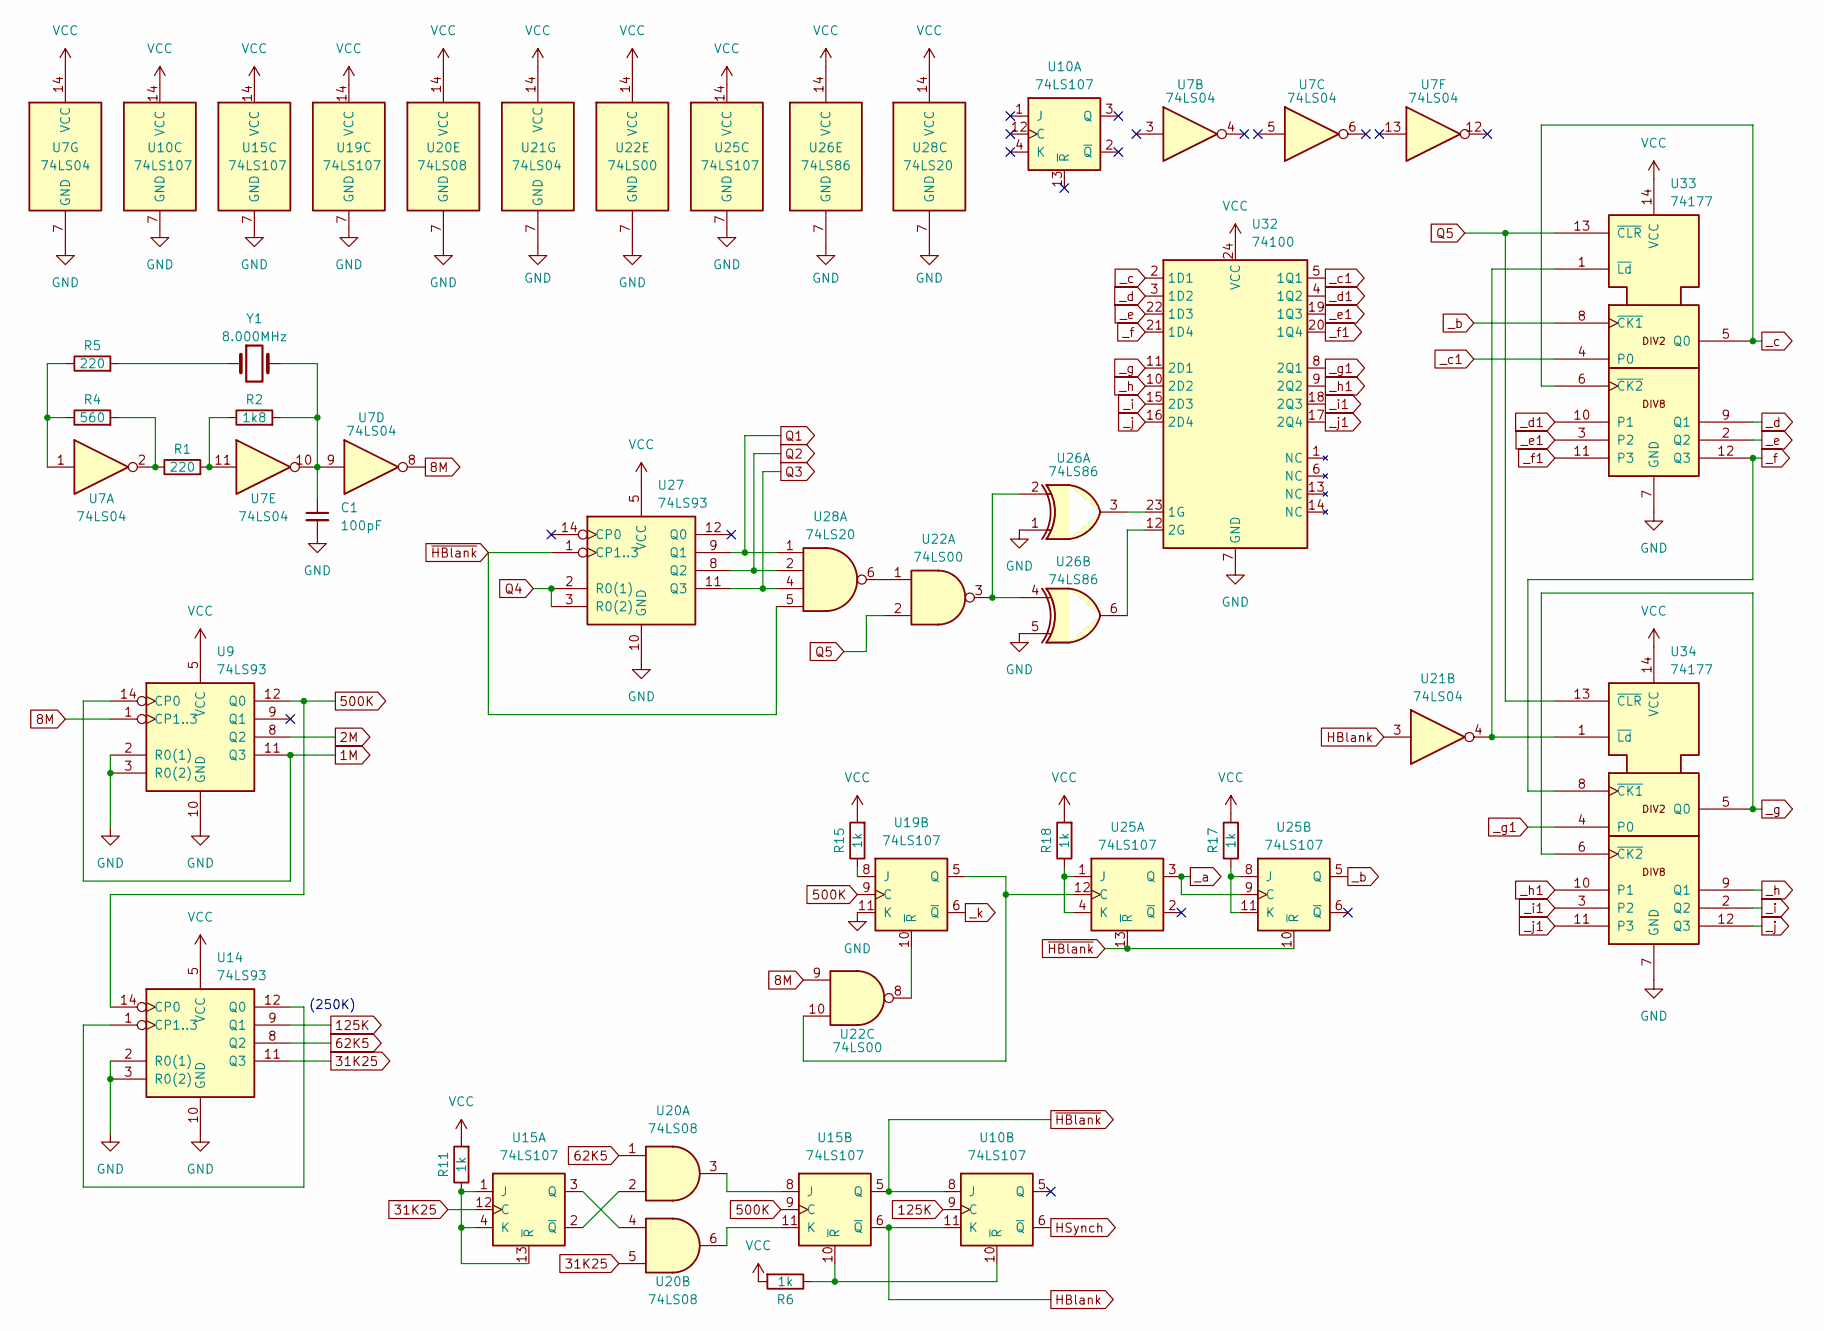
[picture p26: schematic SYNC.kicad_sch]

Parts:
C1: 100pF
R1, R5: 220
R2: 1k8
R4: 560
R6, R11, R15, R17, R18: 1k
U7, U21: 74LS04; DIP-14_W7.62mm
U9, U14, U27: 74LS93; DIP-10_W7.62mm
U10, U15, U19, U25: 74LS107; DIP-14_W7.62mm
U20: 74LS08; DIP-14_W7.62mm
U22: 74LS00; DIP-14_W7.62mm
U26: 74LS86; DIP-14_W7.62mm
U28: 74LS20; DIP-12_W7.62mm
U32: 74100; DIP-24_W15.24mm
U33, U34: 74177
Y1: 8.000MHz

Connections:
1M: U9.11 (Q3), U9.14 (CP0)
2M: U9.8 (Q2)
8M: U7.8, U9.1 (CP1..3), U22.9
31K25: U14.11 (Q3), U15.12 (C), U20.5
62K5: U14.8 (Q2), U20.1
125K: U10.9 (C), U14.9 (Q1)
500K: U9.12 (Q0), U14.14 (CP0), U15.9 (C), U19.9 (C)
GND: C1.2, U7.7 (GND), U9.2 (R0(1)), U9.3 (R0(2)), U9.10 (GND), U10.7 (GND), U14.2 (R0(1)), U14.3 (R0(2)), U14.10 (GND), U15.7 (GND), U19.7 (GND), U19.11 (K), U20.7 (GND), U21.7 (GND), U22.7 (GND), U25.7 (GND), U26.1, U26.5, U26.7 (GND), U27.10 (GND), U28.7 (GND), U32.7 (GND), U33.7 (GND), U34.7 (GND)
HBlank: U10.11 (K), U15.6 (~Q), U21.3
HSynch: U10.6 (~Q)
unnamed: C1.1, R2.2, U7.9, U7.10, Y1.2
unnamed: R1.1, R4.2, U7.2
unnamed: R1.2, R2.1, U7.11
unnamed: R4.1, R5.1, U7.1
unnamed: R5.2, Y1.1
unnamed: R6.1, U10.10 (~R), U15.10 (~R)
unnamed: R11.1, U15.1 (J), U15.4 (K), U15.13 (~R)
unnamed: R15.1, U19.8 (J)
unnamed: R17.1, U25.8 (J), U25.11 (K)
unnamed: R18.1, U25.1 (J), U25.4 (K)
unnamed: U14.1 (CP1..3), U14.12 (Q0)
unnamed: U15.2 (~Q), U20.2
unnamed: U15.3 (Q), U20.4
unnamed: U15.8 (J), U20.3
unnamed: U15.11 (K), U20.6
unnamed: U19.5 (Q), U22.10, U25.12 (C)
unnamed: U19.10 (~R), U22.8
unnamed: U21.4, U33.1 (~Ld), U34.1 (~Ld)
unnamed: U22.1, U28.6
unnamed: U22.3, U26.2, U26.4
unnamed: U26.3, U32.23 (1G)
unnamed: U26.6, U32.12 (2G)
Q1: U27.9 (Q1), U28.1
Q2: U27.8 (Q2), U28.2
Q3: U27.11 (Q3), U28.4
Q4: U27.2 (R0(1)), U27.3 (R0(2))
Q5: U22.2, U33.13 (~CLR), U34.13 (~CLR)
VCC: R6.2, R11.2, R15.2, R17.2, R18.2, U7.14 (VCC), U9.5 (VCC), U10.14 (VCC), U14.5 (VCC), U15.14 (VCC), U19.14 (VCC), U20.14 (VCC), U21.14 (VCC), U22.14 (VCC), U25.14 (VCC), U26.14 (VCC), U27.5 (VCC), U28.14 (VCC), U32.24 (VCC), U33.14 (VCC), U34.14 (VCC)
_a: U25.3 (Q), U25.9 (C)
_b: U25.5 (Q), U33.8 (~CK1)
_c: U32.2 (1D1), U33.5 (Q0), U33.6 (~CK2)
_c1: U32.5 (1Q1), U33.4 (P0)
_d: U32.3 (1D2), U33.9 (Q1)
_d1: U32.4 (1Q2), U33.10 (P1)
_e: U32.22 (1D3), U33.2 (Q2)
_e1: U32.19 (1Q3), U33.3 (P2)
_f: U32.21 (1D4), U33.12 (Q3), U34.8 (~CK1)
_f1: U32.20 (1Q4), U33.11 (P3)
_g: U32.11 (2D1), U34.5 (Q0), U34.6 (~CK2)
_g1: U32.8 (2Q1), U34.4 (P0)
_h: U32.10 (2D2), U34.9 (Q1)
_h1: U32.9 (2Q2), U34.10 (P1)
_i: U32.15 (2D3), U34.2 (Q2)
_i1: U32.18 (2Q3), U34.3 (P2)
_j: U32.16 (2D4), U34.12 (Q3)
_j1: U32.17 (2Q4), U34.11 (P3)
_k: U19.6 (~Q)
~HBlank: U10.8 (J), U15.5 (Q), U25.10 (~R), U25.13 (~R), U27.1 (CP1..3), U28.5

Notes on the sheet:
(250K)
