houmei/MZ-80K/MZ80KiCad/TIMER.kicad_sch

## KiCad design MZ80KiCad/TIMER.kicad_sch (2024-05-27)

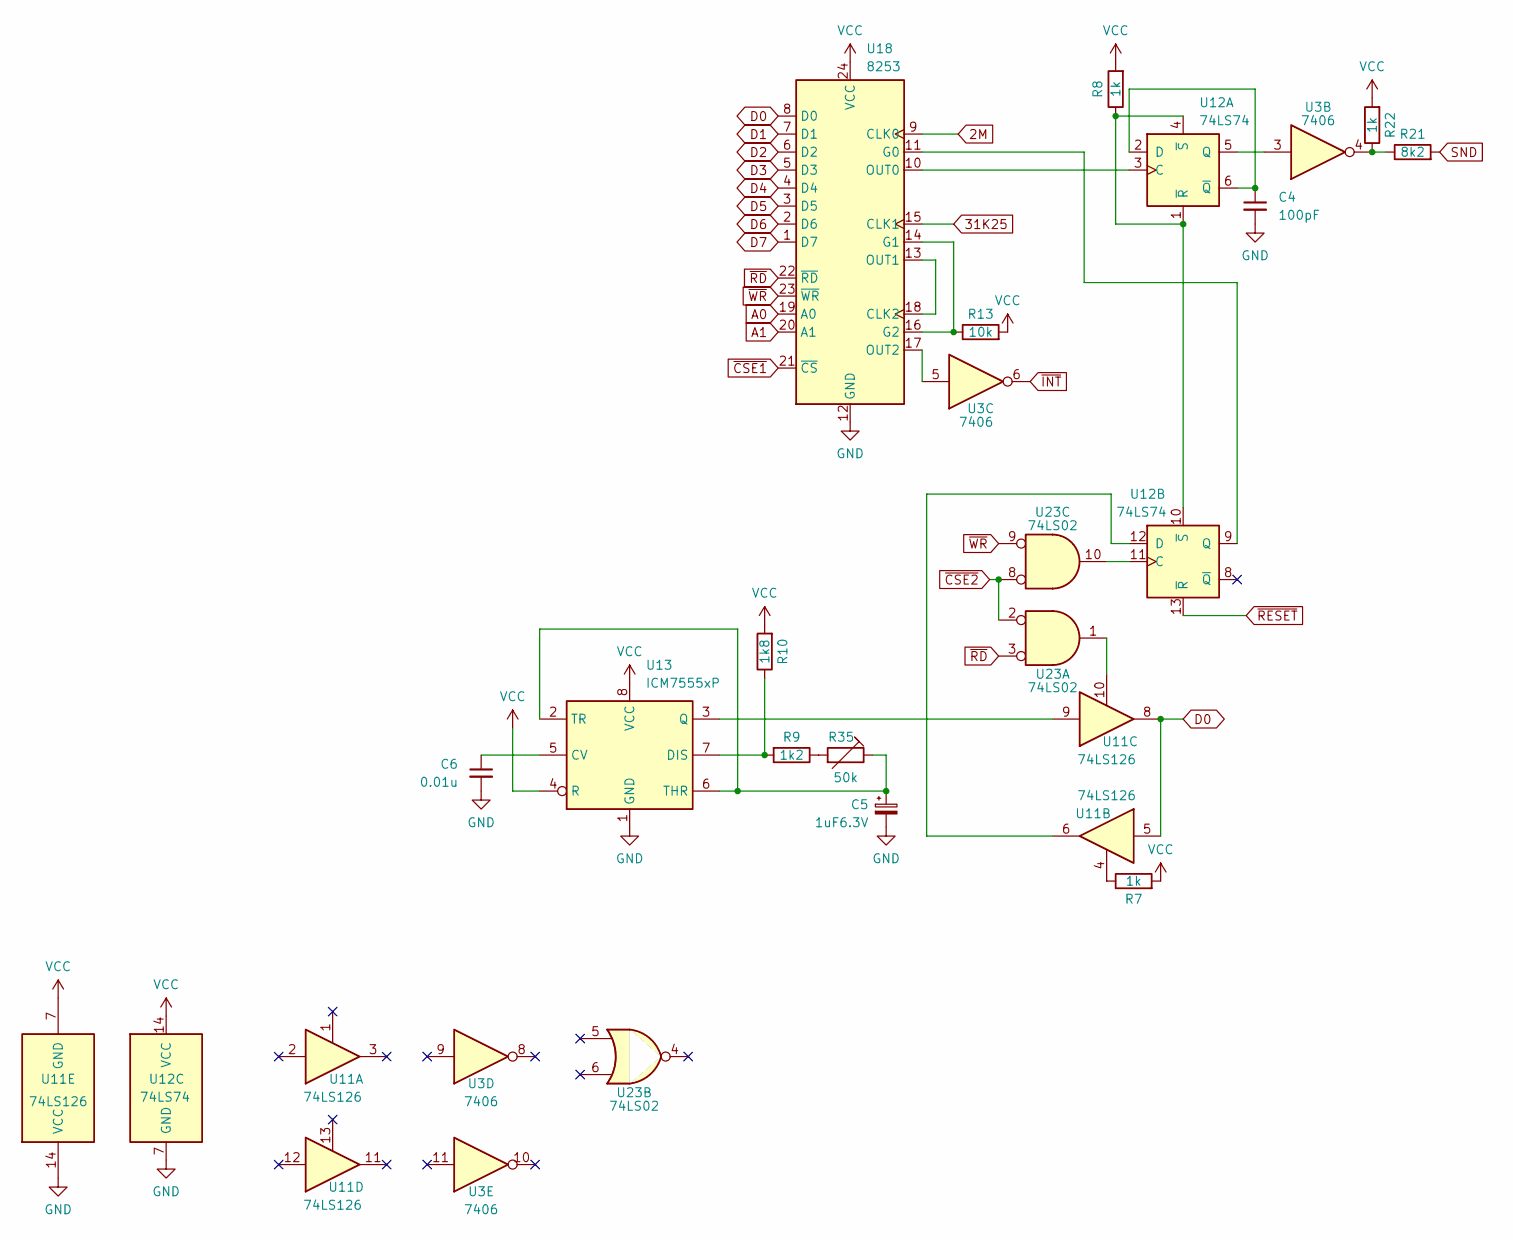
[picture p27: schematic TIMER.kicad_sch]

Parts:
C4: 100pF
C5: 1uF6.3V
C6: 0.01u
R7, R8, R22: 1k
R9: 1k2
R10: 1k8
R13: 10k
R21: 8k2
R35: 50k
U3: 7406; DIP-14_W7.62mm
U11: 74LS126; DIP-14_W7.62mm
U12: 74LS74; DIP-14_W7.62mm
U13: ICM7555xP; DIP-8_W7.62mm
U18: 8253; DIP-24_W15.24mm
U23: 74LS02; DIP-14_W7.62mm

Connections:
2M: U18.9 (CLK0)
31K25: U18.15 (CLK1)
A0: U18.19 (A0)
A1: U18.20 (A1)
D0: U11.5, U11.8, U18.8 (D0)
D1: U18.7 (D1)
D2: U18.6 (D2)
D3: U18.5 (D3)
D4: U18.4 (D4)
D5: U18.3 (D5)
D6: U18.2 (D6)
D7: U18.1 (D7)
GND: C4.2, C5.2, C6.2, U11.14 (VCC), U12.7 (GND), U13.1 (GND), U18.12 (GND)
unnamed: C4.1, U12.2 (D), U12.6 (~Q)
unnamed: C5.1, R35.1, U13.2 (TR), U13.6 (THR)
unnamed: C6.1, U13.5 (CV)
unnamed: R7.1, U11.4
unnamed: R8.1, U12.1 (~R), U12.4 (~S), U12.10 (~S)
unnamed: R9.2, R10.1, U13.7 (DIS)
unnamed: R13.1, U18.14 (G1), U18.16 (G2)
unnamed: R21.1, R22.1, U3.4
unnamed: R9.1, R35.2
unnamed: U11.6, U12.12 (D)
unnamed: U11.9, U13.3 (Q)
unnamed: U11.10, U23.1
unnamed: U12.3 (C), U18.10 (OUT0)
unnamed: U3.3, U12.5 (Q)
unnamed: U12.9 (Q), U18.11 (G0)
unnamed: U12.11 (C), U23.10
unnamed: U18.13 (OUT1), U18.18 (CLK2)
unnamed: U3.5, U18.17 (OUT2)
SND: R21.2
VCC: R7.2, R8.2, R10.2, R13.2, R22.2, U11.7 (GND), U12.14 (VCC), U13.4 (R), U13.8 (VCC), U18.24 (VCC)
~CSE1: U18.21 (~CS)
~CSE2: U23.2, U23.8
~INT: U3.6
~RD: U18.22 (~RD), U23.3
~RESET: U12.13 (~R)
~WR: U18.23 (~WR), U23.9
