houmei/MZ-80K/MZ80KiCad/VGEN.kicad_sch

## KiCad design MZ80KiCad/VGEN.kicad_sch (2024-05-27)

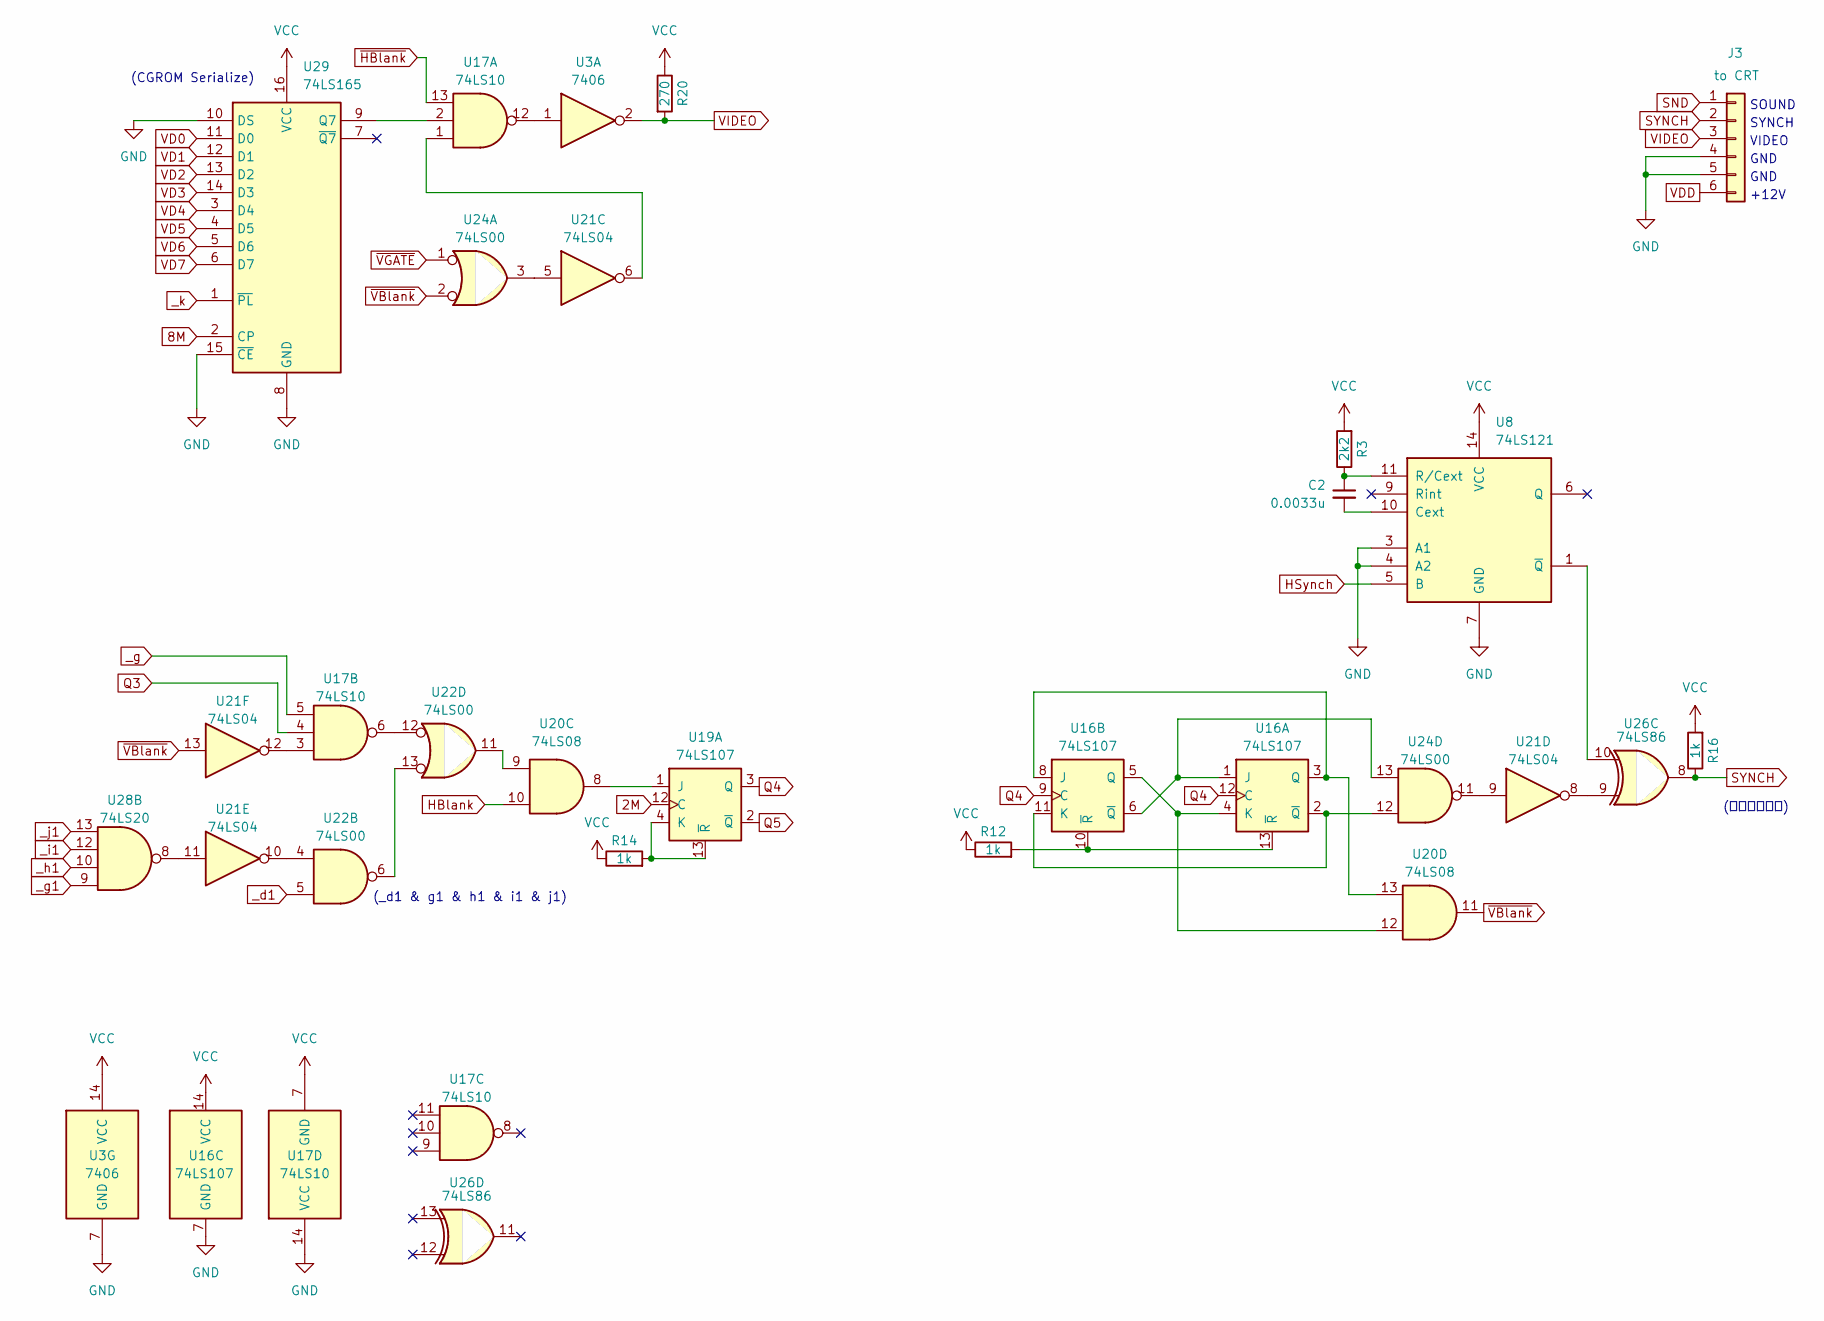
[picture p28: schematic VGEN.kicad_sch]

Parts:
C2: 0.0033u
J3: to CRT; PinHeader_1x06_P2.54mm_Vertical
R3: 2k2
R12, R14, R16: 1k
R20: 270
U3: 7406; DIP-14_W7.62mm
U8: 74LS121; DIP-10_W7.62mm
U16, U19: 74LS107; DIP-14_W7.62mm
U17: 74LS10; DIP-14_W7.62mm
U20: 74LS08; DIP-14_W7.62mm
U21: 74LS04; DIP-14_W7.62mm
U22, U24: 74LS00; DIP-14_W7.62mm
U26: 74LS86; DIP-14_W7.62mm
U28: 74LS20; DIP-12_W7.62mm
U29: 74LS165; DIP-16_W7.62mm

Connections:
2M: U19.12 (C)
8M: U29.2 (CP)
GND: J3.4, J3.5, U3.7 (GND), U8.3 (A1), U8.4 (A2), U8.7 (GND), U16.7 (GND), U17.14 (VCC), U29.8 (GND), U29.10 (DS), U29.15 (~CE)
HBlank: U20.10
HSynch: U8.5 (B)
unnamed: C2.1, R3.1, U8.11 (R/Cext)
unnamed: C2.2, U8.10 (Cext)
unnamed: R12.2, U16.10 (~R), U16.13 (~R)
unnamed: R14.2, U19.4 (K), U19.13 (~R)
unnamed: U16.1 (J), U16.6 (~Q), U24.13
unnamed: U16.3 (Q), U16.8 (J), U20.13
unnamed: U16.4 (K), U16.5 (Q), U20.12
unnamed: U16.2 (~Q), U16.11 (K), U24.12
unnamed: U17.1, U21.6
unnamed: U17.2, U29.9 (Q7)
unnamed: U17.3, U21.12
unnamed: U17.6, U22.12
unnamed: U3.1, U17.12
unnamed: U19.1 (J), U20.8
unnamed: U20.9, U22.11
unnamed: U21.5, U24.3
unnamed: U21.8, U26.9
unnamed: U21.9, U24.11
unnamed: U21.10, U22.4
unnamed: U21.11, U28.8
unnamed: U22.6, U22.13
unnamed: U8.1 (~Q), U26.10
Q3: U17.4
Q4: U16.9 (C), U16.12 (C), U19.3 (Q)
Q5: U19.2 (~Q)
SND: J3.1
SYNCH: J3.2, R16.1, U26.8
VCC: R3.2, R12.1, R14.1, R16.2, R20.1, U3.14 (VCC), U8.14 (VCC), U16.14 (VCC), U17.7 (GND), U29.16 (VCC)
VD0: U29.11 (D0)
VD1: U29.12 (D1)
VD2: U29.13 (D2)
VD3: U29.14 (D3)
VD4: U29.3 (D4)
VD5: U29.4 (D5)
VD6: U29.5 (D6)
VD7: U29.6 (D7)
VDD: J3.6
VIDEO: J3.3, R20.2, U3.2
_d1: U22.5
_g: U17.5
_g1: U28.9
_h1: U28.10
_i1: U28.12
_j1: U28.13
_k: U29.1 (~PL)
~HBlank: U17.13
~VBlank: U20.11, U21.13, U24.2
~VGATE: U24.1

Notes on the sheet:
SOUND
(_d1 & g1 & h1 & i1 & j1)
SYNCH
GND
VIDEO
+12V
(CGROM Serialize)
(複合同期信号)
