houmei/MZ-80K/MZ80KiCad/VRAM.kicad_sch

## KiCad design MZ80KiCad/VRAM.kicad_sch (2024-05-27)

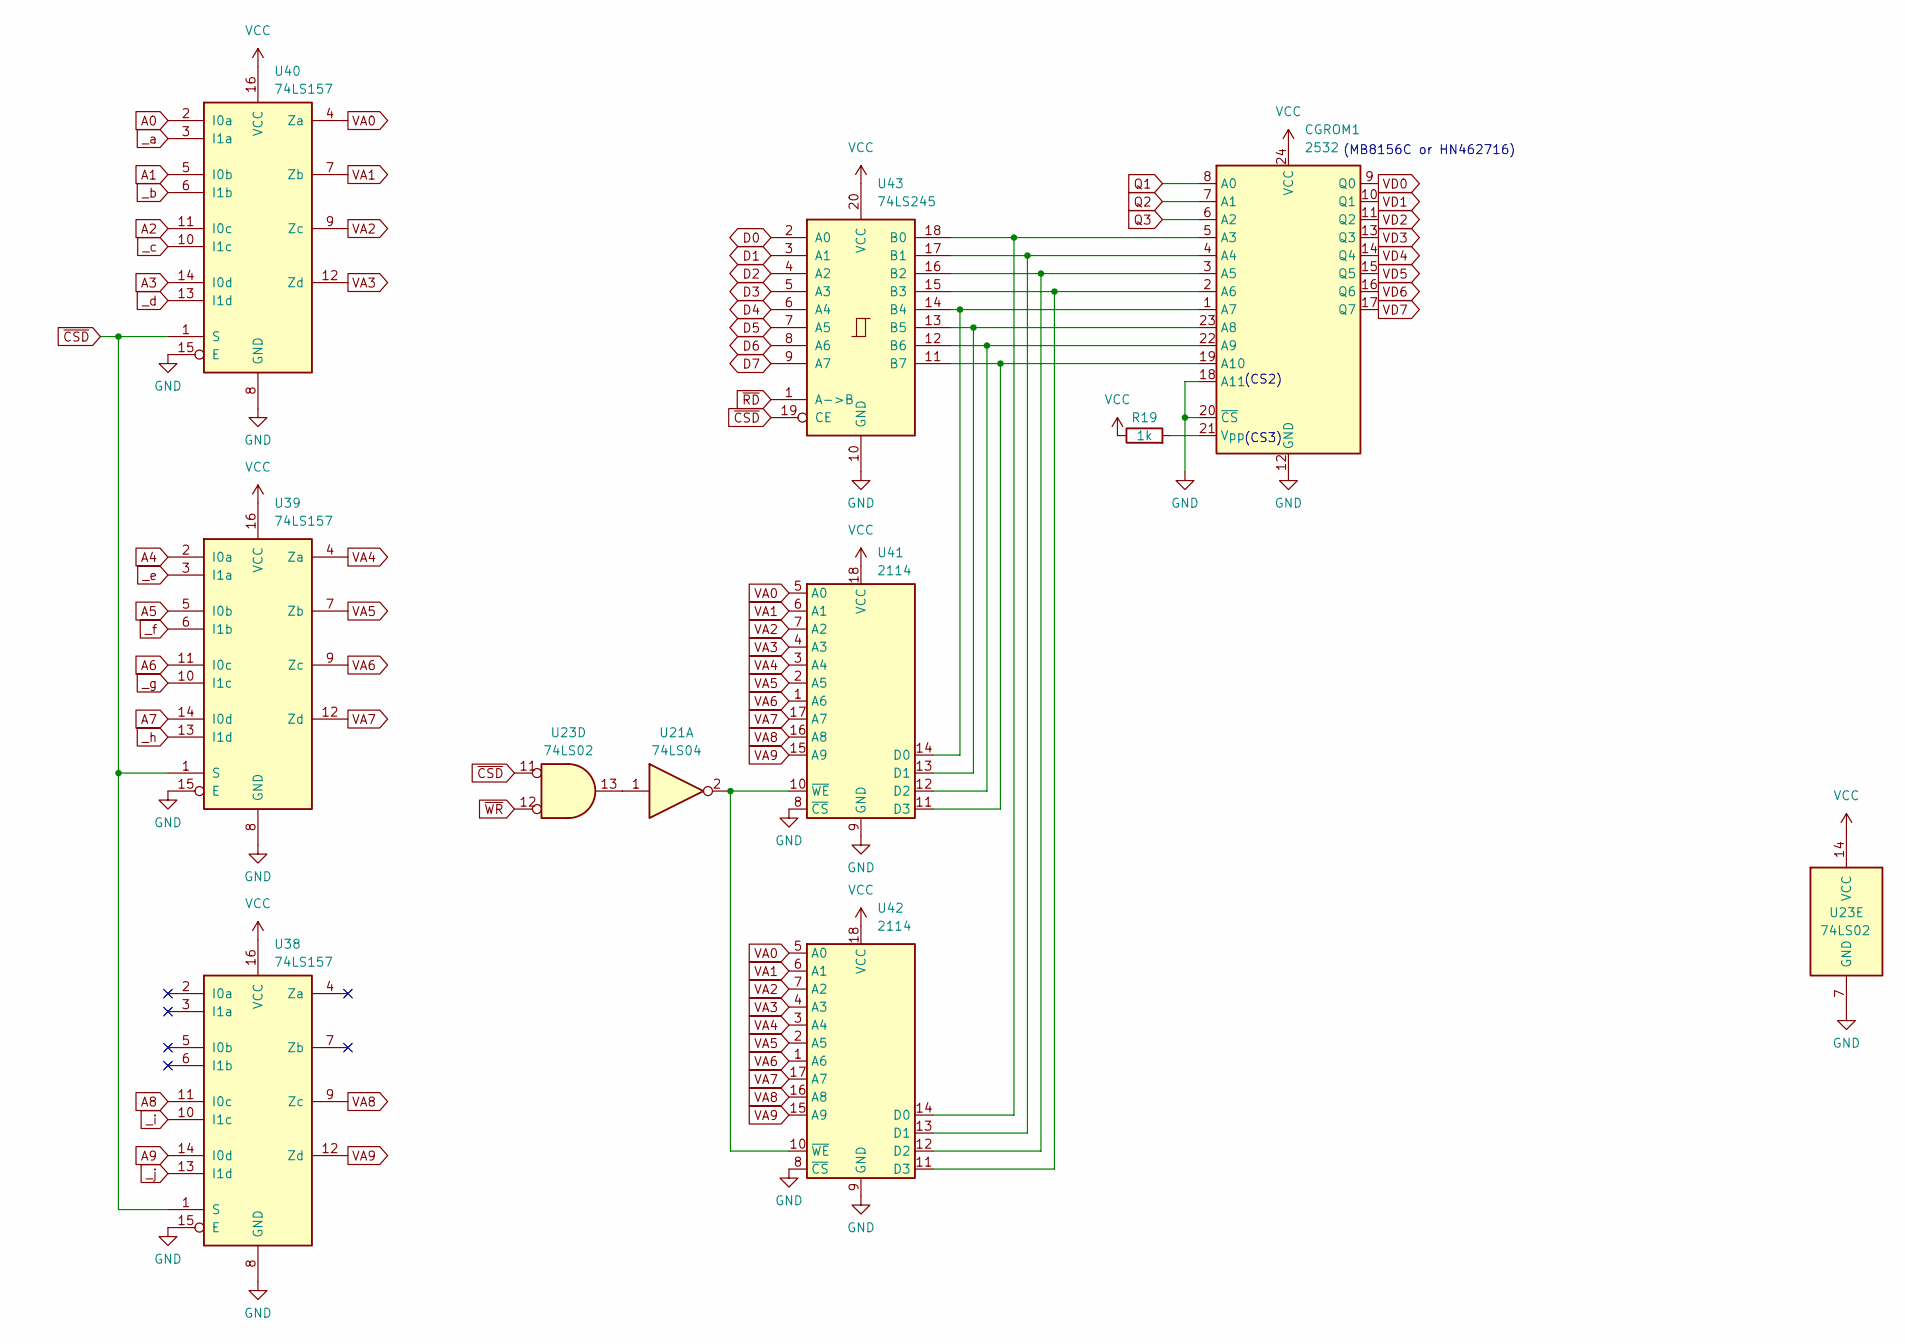
[picture p29: schematic VRAM.kicad_sch]

Parts:
CGROM1: 2532; DIP-24_W15.24mm
R19: 1k
U21: 74LS04; DIP-14_W7.62mm
U23: 74LS02; DIP-14_W7.62mm
U38, U39, U40: 74LS157; DIP-16_W7.62mm
U41, U42: 2114; DIP-18_W7.62mm
U43: 74LS245; DIP-20_W7.62mm

Connections:
A0: U40.2 (I0a)
A1: U40.5 (I0b)
A2: U40.11 (I0c)
A3: U40.14 (I0d)
A4: U39.2 (I0a)
A5: U39.5 (I0b)
A6: U39.11 (I0c)
A7: U39.14 (I0d)
A8: U38.11 (I0c)
A9: U38.14 (I0d)
D0: U43.2 (A0)
D1: U43.3 (A1)
D2: U43.4 (A2)
D3: U43.5 (A3)
D4: U43.6 (A4)
D5: U43.7 (A5)
D6: U43.8 (A6)
D7: U43.9 (A7)
GND: CGROM1.12 (GND), CGROM1.18 (A11), CGROM1.20 (~CS), U23.7 (GND), U38.8 (GND), U38.15 (E), U39.8 (GND), U39.15 (E), U40.8 (GND), U40.15 (E), U41.8 (~CS), U41.9 (GND), U42.8 (~CS), U42.9 (GND), U43.10 (GND)
unnamed: CGROM1.1 (A7), U41.14 (D0), U43.14 (B4)
unnamed: CGROM1.2 (A6), U42.11 (D3), U43.15 (B3)
unnamed: CGROM1.3 (A5), U42.12 (D2), U43.16 (B2)
unnamed: CGROM1.4 (A4), U42.13 (D1), U43.17 (B1)
unnamed: CGROM1.5 (A3), U42.14 (D0), U43.18 (B0)
unnamed: CGROM1.19 (A10), U41.11 (D3), U43.11 (B7)
unnamed: CGROM1.21 (Vpp), R19.2
unnamed: CGROM1.22 (A9), U41.12 (D2), U43.12 (B6)
unnamed: CGROM1.23 (A8), U41.13 (D1), U43.13 (B5)
unnamed: U21.1, U23.13
unnamed: U21.2, U41.10 (~WE), U42.10 (~WE)
Q1: CGROM1.8 (A0)
Q2: CGROM1.7 (A1)
Q3: CGROM1.6 (A2)
VA0: U40.4 (Za), U41.5 (A0), U42.5 (A0)
VA1: U40.7 (Zb), U41.6 (A1), U42.6 (A1)
VA2: U40.9 (Zc), U41.7 (A2), U42.7 (A2)
VA3: U40.12 (Zd), U41.4 (A3), U42.4 (A3)
VA4: U39.4 (Za), U41.3 (A4), U42.3 (A4)
VA5: U39.7 (Zb), U41.2 (A5), U42.2 (A5)
VA6: U39.9 (Zc), U41.1 (A6), U42.1 (A6)
VA7: U39.12 (Zd), U41.17 (A7), U42.17 (A7)
VA8: U38.9 (Zc), U41.16 (A8), U42.16 (A8)
VA9: U38.12 (Zd), U41.15 (A9), U42.15 (A9)
VCC: CGROM1.24 (VCC), R19.1, U23.14 (VCC), U38.16 (VCC), U39.16 (VCC), U40.16 (VCC), U41.18 (VCC), U42.18 (VCC), U43.20 (VCC)
VD0: CGROM1.9 (Q0)
VD1: CGROM1.10 (Q1)
VD2: CGROM1.11 (Q2)
VD3: CGROM1.13 (Q3)
VD4: CGROM1.14 (Q4)
VD5: CGROM1.15 (Q5)
VD6: CGROM1.16 (Q6)
VD7: CGROM1.17 (Q7)
_a: U40.3 (I1a)
_b: U40.6 (I1b)
_c: U40.10 (I1c)
_d: U40.13 (I1d)
_e: U39.3 (I1a)
_f: U39.6 (I1b)
_g: U39.10 (I1c)
_h: U39.13 (I1d)
_i: U38.10 (I1c)
_j: U38.13 (I1d)
~CSD: U23.11, U38.1 (S), U39.1 (S), U40.1 (S), U43.19 (CE)
~RD: U43.1 (A->B)
~WR: U23.12

Notes on the sheet:
(MB8156C or HN462716)
(CS2)
(CS3)
