houmei/MZ-80K/MZ80KiCad/decoder.kicad_sch

## KiCad design MZ80KiCad/decoder.kicad_sch (2024-05-27)

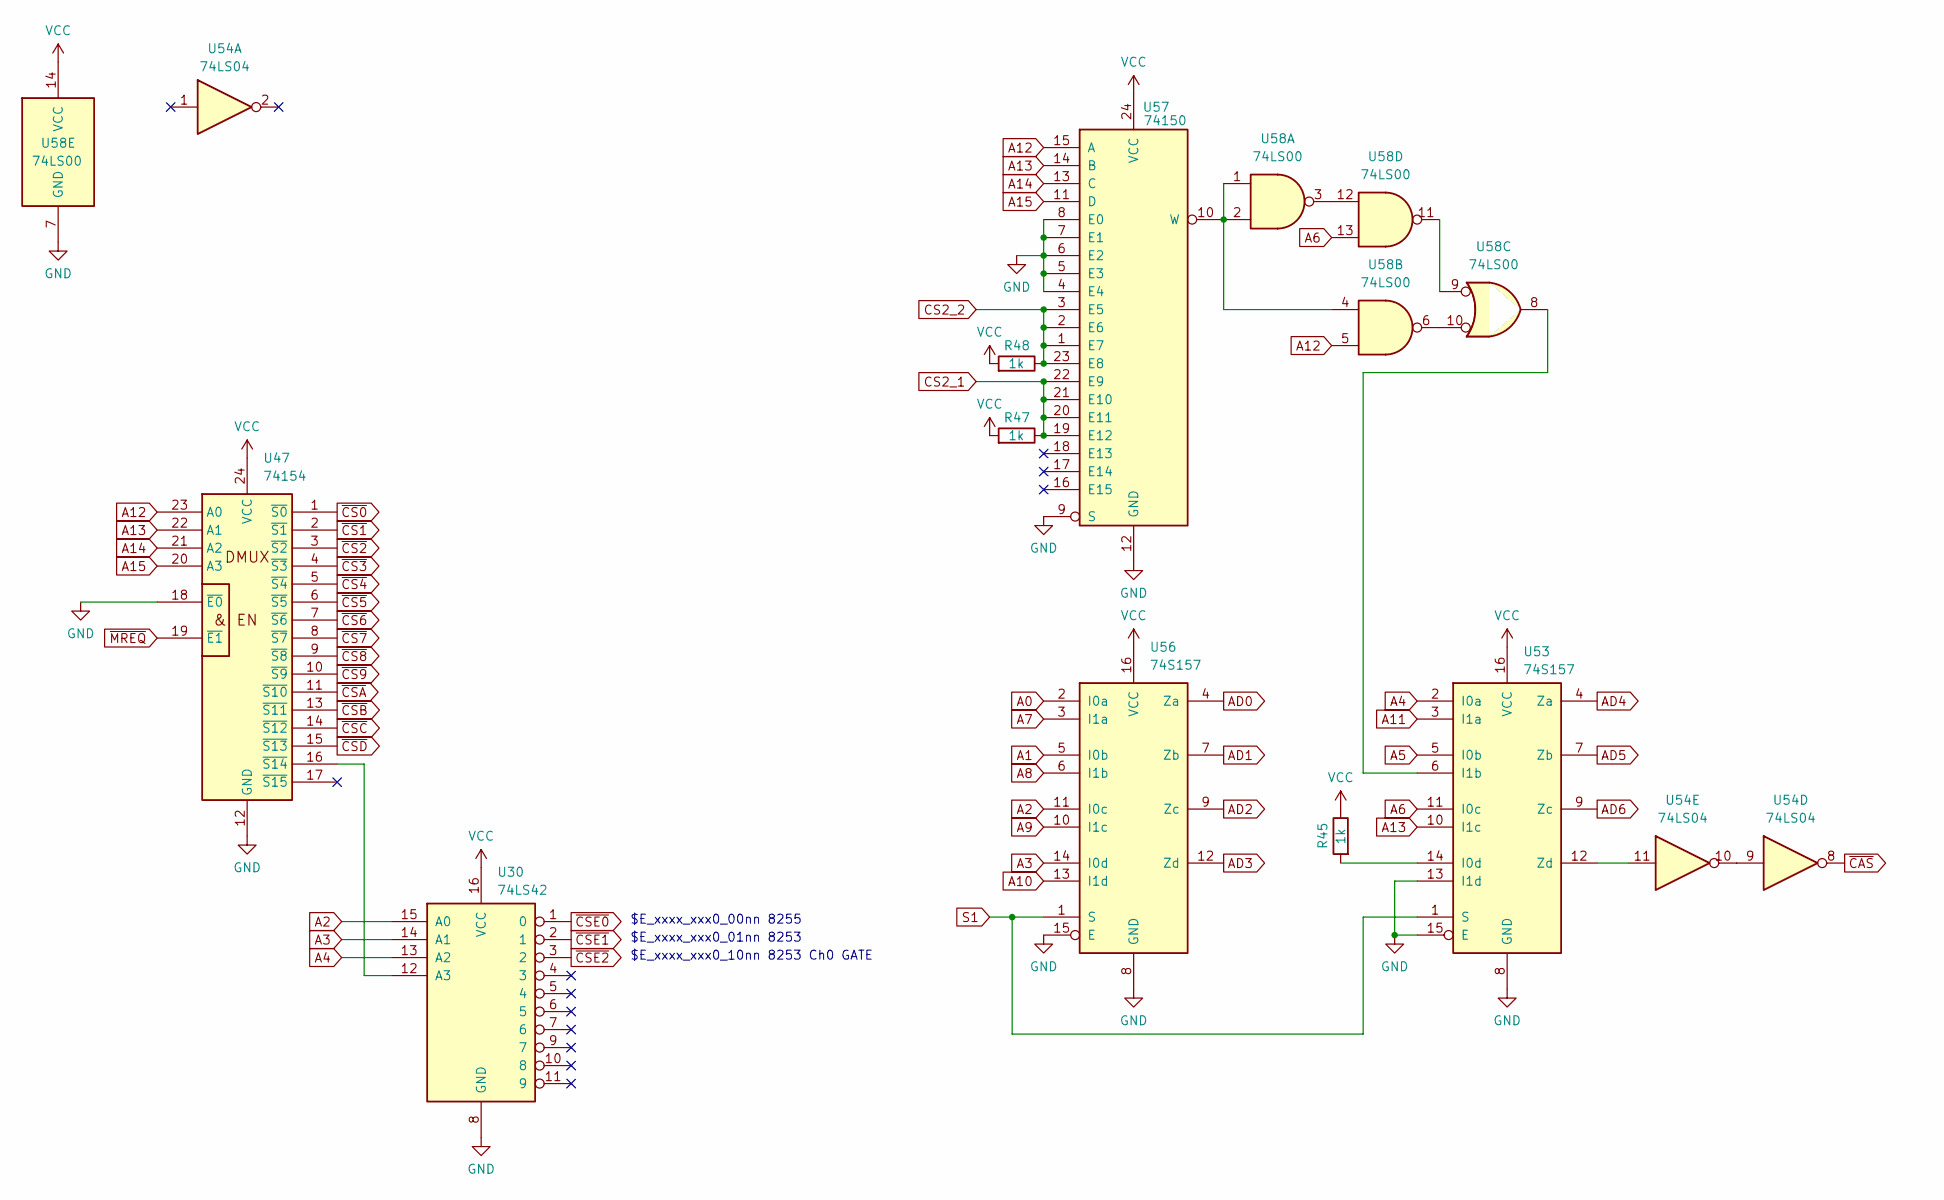
[picture p30: schematic decoder.kicad_sch]

Parts:
R45, R47, R48: 1k
U30: 74LS42; DIP-16_W7.62mm
U47: 74154
U53, U56: 74S157; DIP-16_W7.62mm
U54: 74LS04; DIP-14_W7.62mm
U57: 74150
U58: 74LS00; DIP-14_W7.62mm

Connections:
A0: U56.2 (I0a)
A1: U56.5 (I0b)
A2: U30.15 (A0), U56.11 (I0c)
A3: U30.14 (A1), U56.14 (I0d)
A4: U30.13 (A2), U53.2 (I0a)
A5: U53.5 (I0b)
A6: U53.11 (I0c), U58.13
A7: U56.3 (I1a)
A8: U56.6 (I1b)
A9: U56.10 (I1c)
A10: U56.13 (I1d)
A11: U53.3 (I1a)
A12: U47.23 (A0), U57.15 (A), U58.5
A13: U47.22 (A1), U53.10 (I1c), U57.14 (B)
A14: U47.21 (A2), U57.13 (C)
A15: U47.20 (A3), U57.11 (D)
AD0: U56.4 (Za)
AD1: U56.7 (Zb)
AD2: U56.9 (Zc)
AD3: U56.12 (Zd)
AD4: U53.4 (Za)
AD5: U53.7 (Zb)
AD6: U53.9 (Zc)
CS2_1: R47.1, U57.19 (E12), U57.20 (E11), U57.21 (E10), U57.22 (E9)
CS2_2: R48.1, U57.1 (E7), U57.2 (E6), U57.3 (E5), U57.23 (E8)
GND: U30.8 (GND), U47.12 (GND), U47.18 (~E0), U53.8 (GND), U53.13 (I1d), U53.15 (E), U56.8 (GND), U56.15 (E), U57.4 (E4), U57.5 (E3), U57.6 (E2), U57.7 (E1), U57.8 (E0), U57.9 (S), U57.12 (GND), U58.7 (GND)
unnamed: R45.2, U53.14 (I0d)
unnamed: U30.12 (A3), U47.16 (~S14)
unnamed: U53.6 (I1b), U58.8
unnamed: U53.12 (Zd), U54.11
unnamed: U54.9, U54.10
unnamed: U57.10 (W), U58.1, U58.2, U58.4
unnamed: U58.6, U58.10
unnamed: U58.9, U58.11
unnamed: U58.3, U58.12
S1: U53.1 (S), U56.1 (S)
VCC: R45.1, R47.2, R48.2, U30.16 (VCC), U47.24 (VCC), U53.16 (VCC), U56.16 (VCC), U57.24 (VCC), U58.14 (VCC)
~CAS: U54.8
~CS0: U47.1 (~S0)
~CS1: U47.2 (~S1)
~CS2: U47.3 (~S2)
~CS3: U47.4 (~S3)
~CS4: U47.5 (~S4)
~CS5: U47.6 (~S5)
~CS6: U47.7 (~S6)
~CS7: U47.8 (~S7)
~CS8: U47.9 (~S8)
~CS9: U47.10 (~S9)
~CSA: U47.11 (~S10)
~CSB: U47.13 (~S11)
~CSC: U47.14 (~S12)
~CSD: U47.15 (~S13)
~CSE0: U30.1 (0)
~CSE1: U30.2 (1)
~CSE2: U30.3 (2)
~MREQ: U47.19 (~E1)

Notes on the sheet:
$E_xxxx_xxx0_01nn 8253
$E_xxxx_xxx0_10nn 8253 Ch0 GATE
$E_xxxx_xxx0_00nn 8255
