houmei/MZ-80K/MZ80KiCad/ramselect.kicad_sch

## KiCad design MZ80KiCad/ramselect.kicad_sch (2023-08-20)

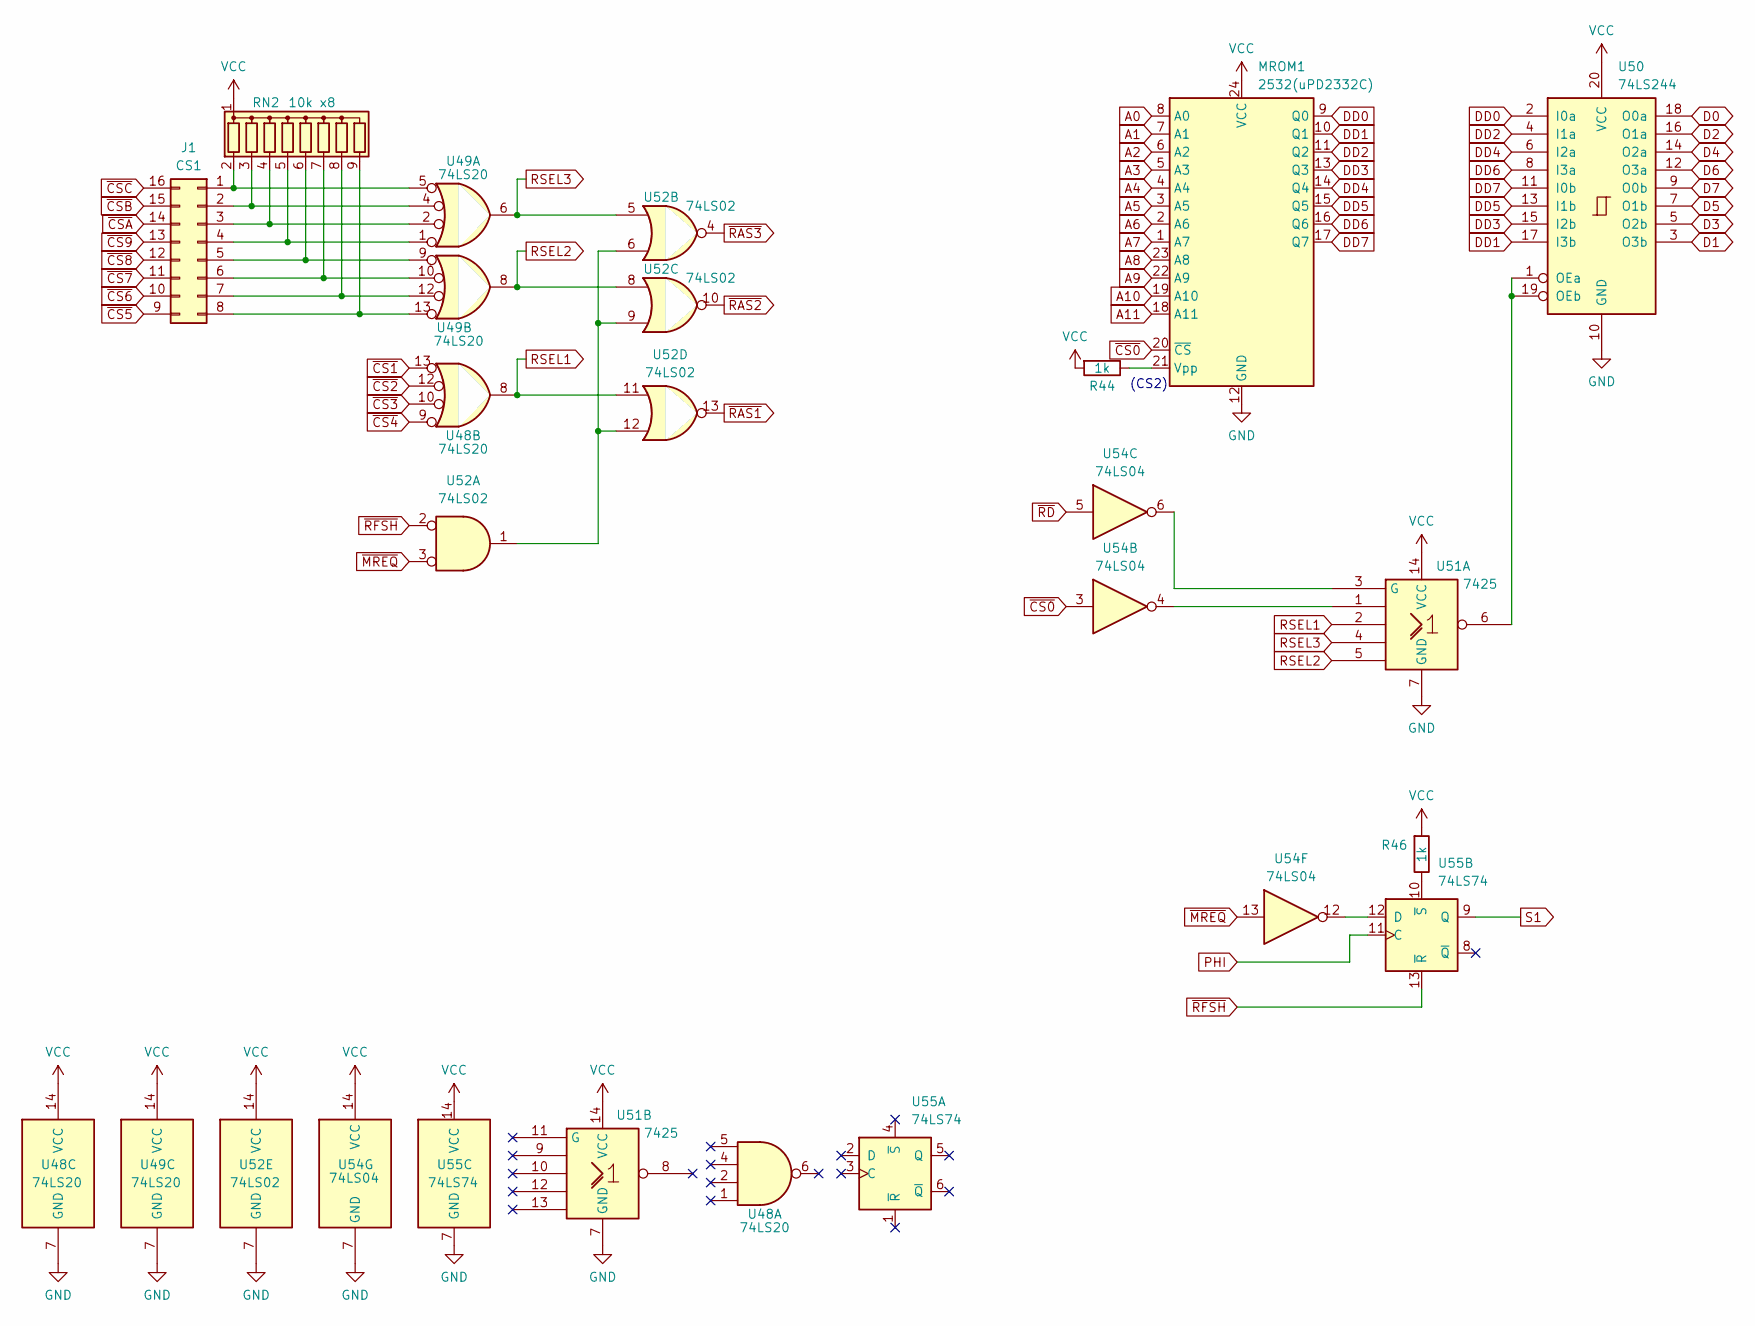
[picture p31: schematic ramselect.kicad_sch]

Parts:
J1: CS1
MROM1: 2532(uPD2332C); DIP-24_W15.24mm
R44, R46: 1k
RN2: 10k x8; R_Array_SIP9
U48, U49: 74LS20; DIP-12_W7.62mm
U50: 74LS244; DIP-20_W7.62mm
U51: 7425; DIP-14_W7.62mm
U52: 74LS02; DIP-14_W7.62mm
U54: 74LS04; DIP-14_W7.62mm
U55: 74LS74; DIP-14_W7.62mm

Connections:
A0: MROM1.8 (A0)
A1: MROM1.7 (A1)
A2: MROM1.6 (A2)
A3: MROM1.5 (A3)
A4: MROM1.4 (A4)
A5: MROM1.3 (A5)
A6: MROM1.2 (A6)
A7: MROM1.1 (A7)
A8: MROM1.23 (A8)
A9: MROM1.22 (A9)
A10: MROM1.19 (A10)
A11: MROM1.18 (A11)
D0: U50.18 (O0a)
D1: U50.3 (O3b)
D2: U50.16 (O1a)
D3: U50.5 (O2b)
D4: U50.14 (O2a)
D5: U50.7 (O1b)
D6: U50.12 (O3a)
D7: U50.9 (O0b)
DD0: MROM1.9 (Q0), U50.2 (I0a)
DD1: MROM1.10 (Q1), U50.17 (I3b)
DD2: MROM1.11 (Q2), U50.4 (I1a)
DD3: MROM1.13 (Q3), U50.15 (I2b)
DD4: MROM1.14 (Q4), U50.6 (I2a)
DD5: MROM1.15 (Q5), U50.13 (I1b)
DD6: MROM1.16 (Q6), U50.8 (I3a)
DD7: MROM1.17 (Q7), U50.11 (I0b)
GND: MROM1.12 (GND), U48.7 (GND), U49.7 (GND), U50.10 (GND), U51.7 (GND), U52.7 (GND), U54.7 (GND), U55.7 (GND)
unnamed: J1.1, RN2.2 (R1), U49.5
unnamed: J1.2, RN2.3 (R2), U49.4
unnamed: J1.3, RN2.4 (R3), U49.2
unnamed: J1.4, RN2.5 (R4), U49.1
unnamed: J1.5, RN2.6 (R5), U49.9
unnamed: J1.6, RN2.7 (R6), U49.10
unnamed: J1.7, RN2.8 (R7), U49.12
unnamed: J1.8, RN2.9 (R8), U49.13
unnamed: MROM1.21 (Vpp), R44.1
unnamed: R46.1, U55.10 (~S)
unnamed: U50.1 (OEa), U50.19 (OEb), U51.6
unnamed: U51.1, U54.4
unnamed: U51.3 (G), U54.6
unnamed: U52.1, U52.6, U52.9, U52.12
unnamed: U54.12, U55.12 (D)
PHI: U55.11 (C)
RSEL1: U48.8, U51.2, U52.11
RSEL2: U49.8, U51.5, U52.8
RSEL3: U49.6, U51.4, U52.5
S1: U55.9 (Q)
VCC: MROM1.24 (VCC), R44.2, R46.2, RN2.1 (common), U48.14 (VCC), U49.14 (VCC), U50.20 (VCC), U51.14 (VCC), U52.14 (VCC), U54.14 (VCC), U55.14 (VCC)
~CS0: MROM1.20 (~CS), U54.3
~CS1: U48.13
~CS2: U48.12
~CS3: U48.10
~CS4: U48.9
~CS5: J1.9
~CS6: J1.10
~CS7: J1.11
~CS8: J1.12
~CS9: J1.13
~CSA: J1.14
~CSB: J1.15
~CSC: J1.16
~MREQ: U52.3, U54.13
~RAS1: U52.13
~RAS2: U52.10
~RAS3: U52.4
~RD: U54.5
~RFSH: U52.2, U55.13 (~R)

Notes on the sheet:
(CS2)
